ultimate/F-OR1/Teilnehmer/ultimate/V1 - 3Wheeler/Antrieb.SLDASM

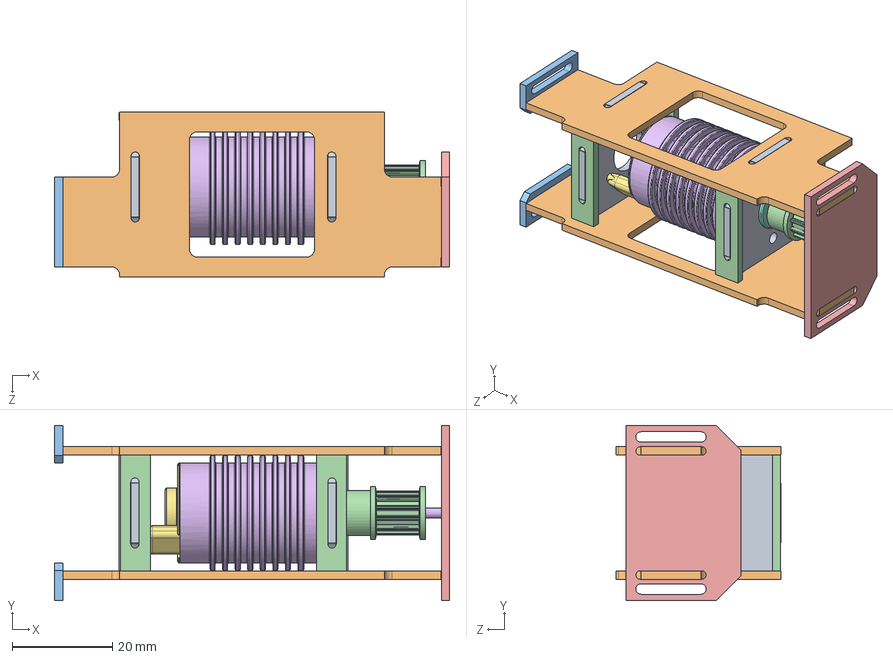
[picture p28: CAD file, 2019-10-27]
Teilnehmer/ultimate/V1 - 3Wheeler/Antrieb.SLDASM
79.0 x 35.0 x 33.0 mm
Rahmen-Antrieb-Platine-Seite x 2
Rahmen-Antrieb-Platine-Oben x 2
Rahmen-Antrieb-Platine-Anschluss2 x 2
Rahmen-Antrieb-Platine-Hinten x 4
Rahmen-Antrieb-Platine-Anschluss1
Motor_B20-30-24S-FIN-Gehaeuse
Motor_B20-30-24S-FIN-FlanschHinten
Motor_B20-30-24S-FIN-FlanschVorne
Motor_B20-30-24S-FIN-Rotorwelle
Motor_B20-30-24S-FIN-Lager x 2
Motor_B20-30-24S-FIN-Masse
Zahnriemenrad T2.5 B6 bis Z20
Antrieb-Reduzierhülse
Antrieb-Dorn
