ultimate/F-OR1/Teilnehmer/ultimate/V1 - 3Wheeler/Fertigung/Rahmen-Antrieb-Flach.SLDASM

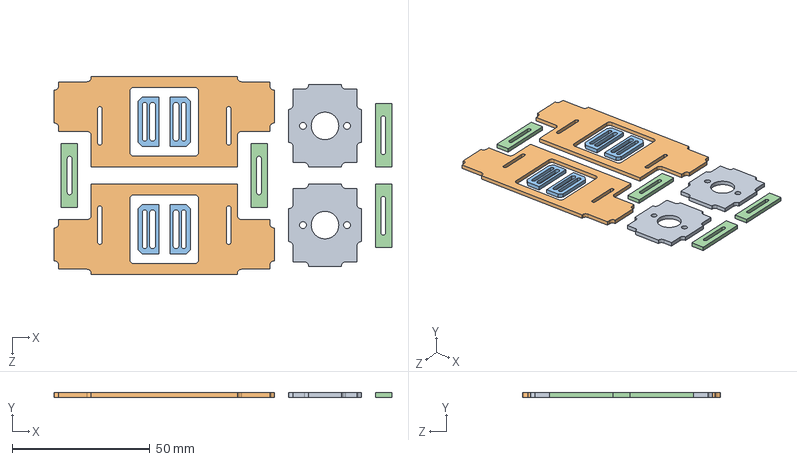
[picture p29: CAD file, 2019-10-27]
Teilnehmer/ultimate/V1 - 3Wheeler/Fertigung/Rahmen-Antrieb-Flach.SLDASM
122.6 x 1.65 x 72.0 mm
Rahmen-Antrieb-Platine-Seite x 2
Rahmen-Antrieb-Platine-Oben x 2
Rahmen-Antrieb-Platine-Anschluss2 x 4
Rahmen-Antrieb-Platine-Hinten x 4
