ultimate/F-OR1/Teilnehmer/ultimate/V2 - Lego/Adapter-Servo-Zahnrad-16Z.SLDASM

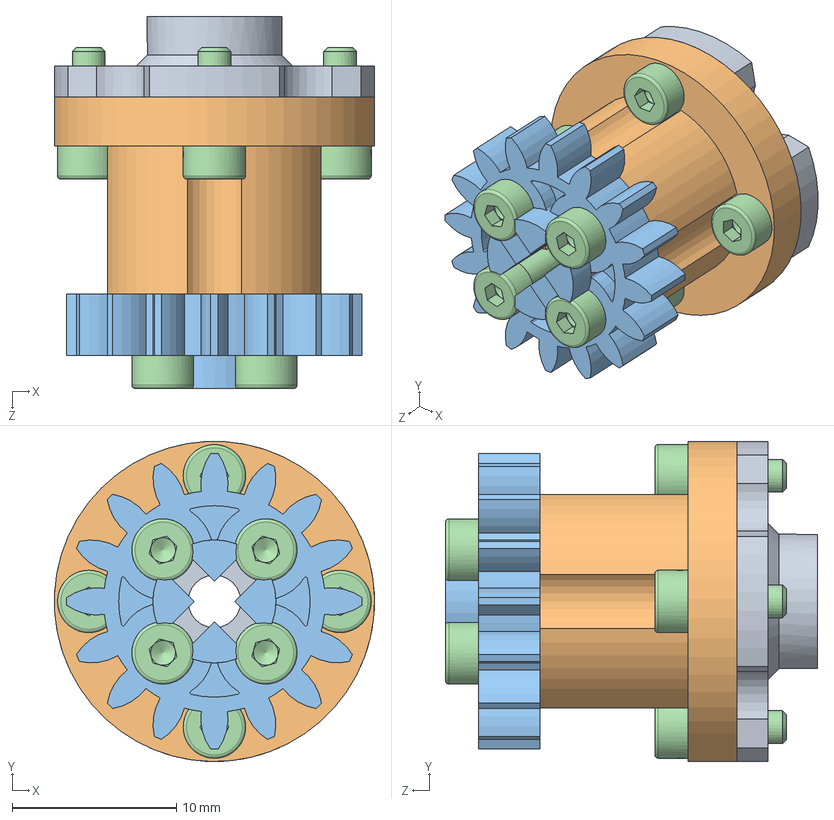
[picture p30: CAD file, 2019-10-27]
Teilnehmer/ultimate/V2 - Lego/Adapter-Servo-Zahnrad-16Z.SLDASM
19.5 x 19.5 x 22.6 mm
Servo-Horn-4er-modifiziert
Adapter-Servo-Zahnrad-16Z
Lego Zahnrad 16Z
DIN 912 M2 x 6 --- 6N x 8
