ultimate/F-OR1/Teilnehmer/ultimate/Test/Kardan.SLDASM

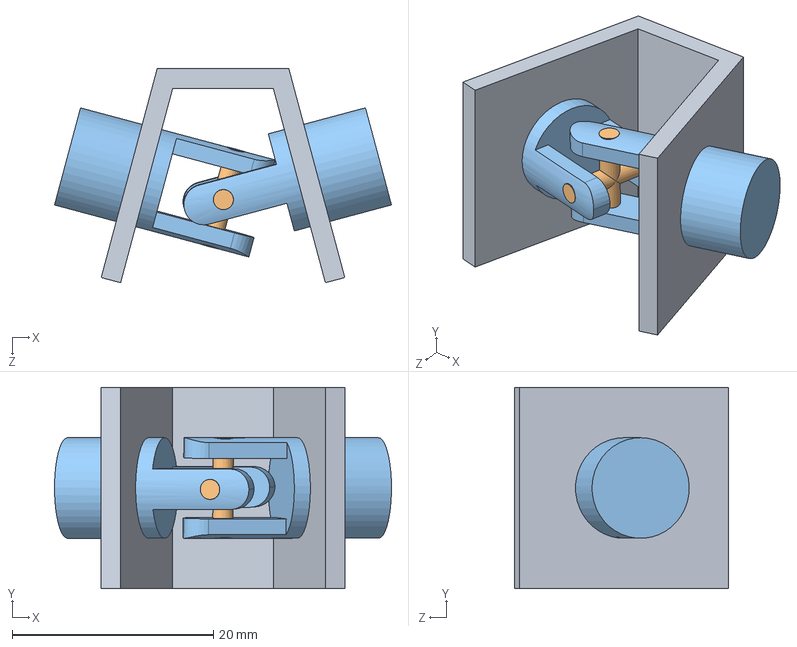
[picture p31: CAD file, 2019-10-27]
Teilnehmer/ultimate/Test/Kardan.SLDASM
33.5 x 20.0 x 21.3 mm
Kardan-Block
Kardan-1
Kardan-2 x 2
