ultimate/F-OR1/Teilnehmer/ultimate/V3 - 4Wheeler/Antrieb.SLDASM

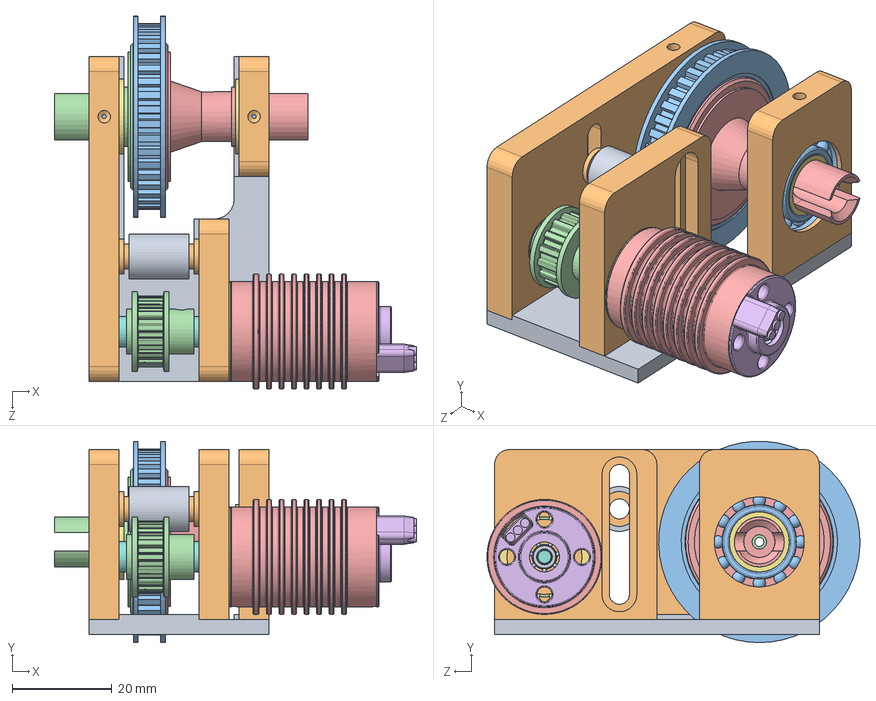
[picture p32: CAD file, 2019-10-27]
Teilnehmer/ultimate/V3 - 4Wheeler/Antrieb.SLDASM
72.4 x 40.3 x 74.6 mm
Antrieb-Rahmen
Antrieb-Lagerbock x 3
Kugellager - 61801 6801 x 2
Kugellager - MR106 x 2
Motor_B20-30-24S-FIN-Gehaeuse
Motor_B20-30-24S-FIN-FlanschHinten
Motor_B20-30-24S-FIN-FlanschVorne
Motor_B20-30-24S-FIN-Rotorwelle
Motor_B20-30-24S-FIN-Lager x 2
Motor_B20-30-24S-FIN-Masse
Kugel-Diff Hobbyking Mission-D Riemenrad
Kugel-Diff Hobbyking Mission-D Achse1
Kugel-Diff Hobbyking Mission-D Achse2
Kugel-Diff Hobbyking Mission-D Laufscheibe x 2
Antrieb-Achse-Lagerhülse x 2
Antrieb-Motorwelle
Antrieb-Spanner-Rolle
Antrieb-Spanner-Lagerhülse x 3
Kugellager - MR74 x 2
Riemenrad Hobbyking Mission-D
