ultimate/F-OR1/Teilnehmer/ultimate/V3 - 4Wheeler/Fertigung/Fraesen1.SLDASM

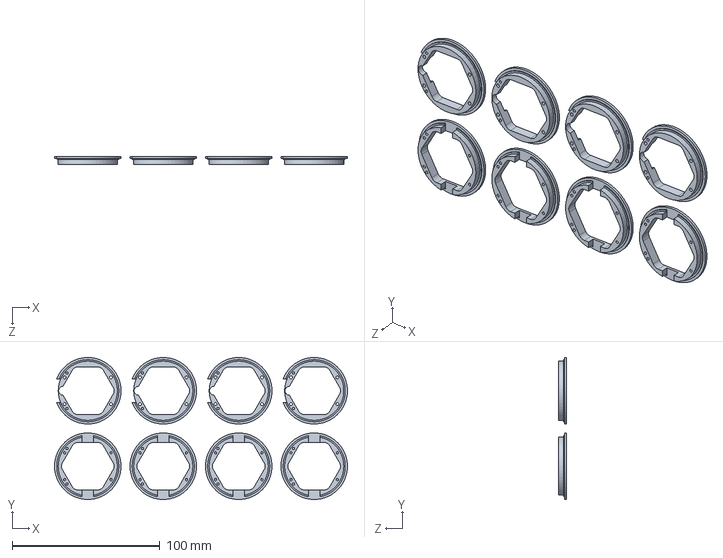
[picture p33: CAD file, 2019-10-27]
Teilnehmer/ultimate/V3 - 4Wheeler/Fertigung/Fraesen1.SLDASM
198.0 x 96.0 x 5.50 mm
Rad-Nabe x 8
