ultimate/F-OR1/Teilnehmer/ultimate/V1 - 3Wheeler/Antrieb-B.SLDASM

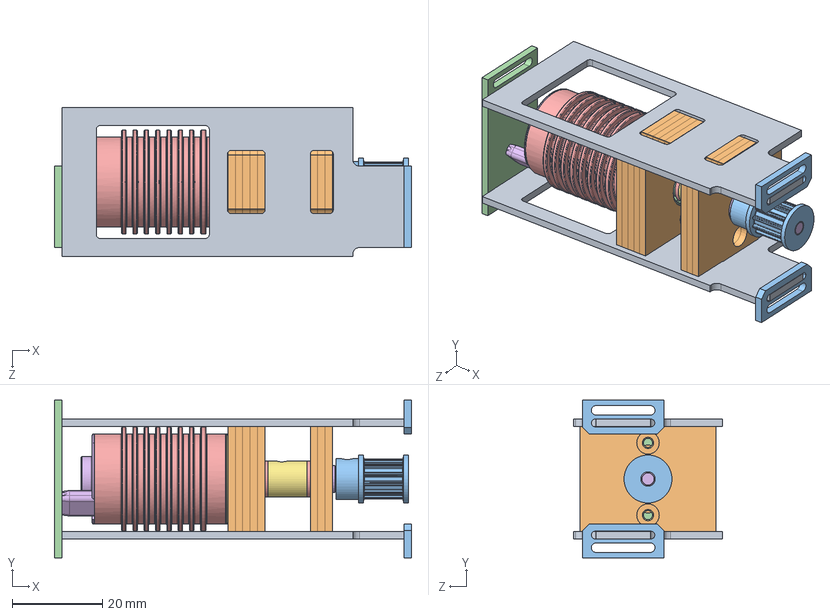
[picture p34: CAD file, 2019-10-27]
Teilnehmer/ultimate/V1 - 3Wheeler/Antrieb-B.SLDASM
79.0 x 34.9 x 33.0 mm
Rahmen-Antrieb-B-Platine-Oben x 2
Rahmen-Antrieb-B-Platine-Seite x 8
Rahmen-Antrieb-B-Platine-Anschluss2 x 2
Rahmen-Antrieb-B-Platine-Anschluss1
Motor_B20-30-24S-FIN-Gehaeuse
Motor_B20-30-24S-FIN-FlanschHinten
Motor_B20-30-24S-FIN-FlanschVorne
Motor_B20-30-24S-FIN-Rotorwelle
Motor_B20-30-24S-FIN-Lager x 2
Motor_B20-30-24S-FIN-Masse
Zahnriemenrad T2.5 B6 bis Z20
Kugellager - MR106 x 2
Antrieb-Passscheibe x 2
Antrieb-B-Welle
Antrieb-B-Passhülse
