ultimate/F-OR1/Teilnehmer/ultimate/Test/Reibrad.SLDASM

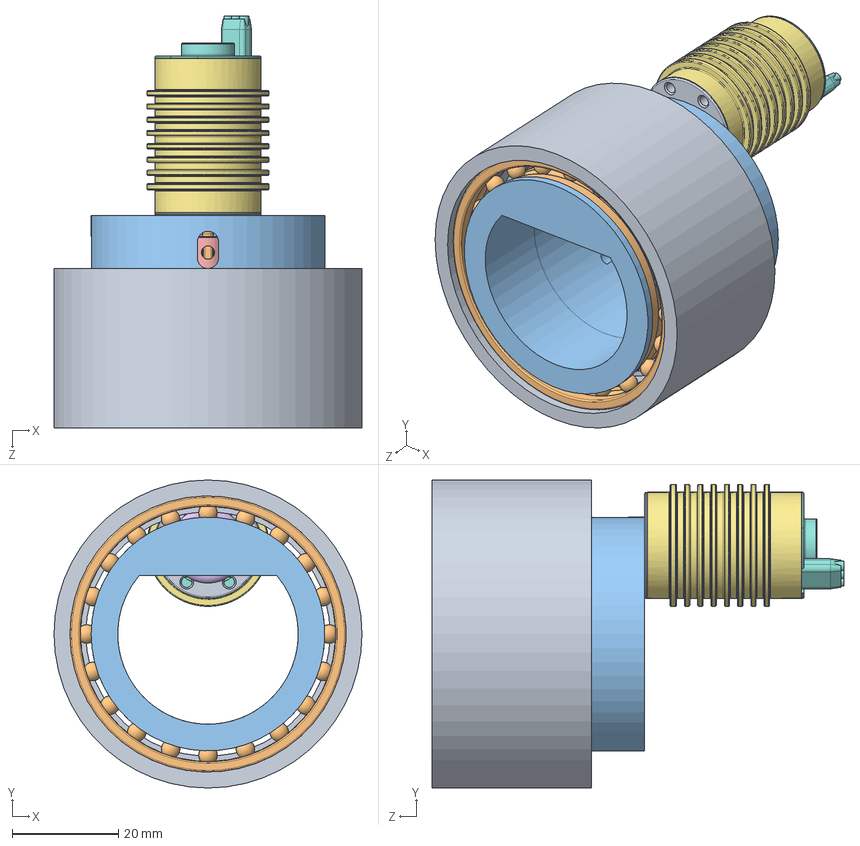
[picture p35: CAD file, 2019-10-27]
Teilnehmer/ultimate/Test/Reibrad.SLDASM
58.0 x 58.0 x 77.5 mm
Reibrad Außenring
Kugellager - 61808 6808 x 2
Reibrad Innenring x 2
Kugellager - MR106 x 2
Reibrad Welle
Reibrad O-Ring
Motor_B20-30-24S-FIN-Gehaeuse
Motor_B20-30-24S-FIN-FlanschHinten
Motor_B20-30-24S-FIN-FlanschVorne
Motor_B20-30-24S-FIN-Rotorwelle
Motor_B20-30-24S-FIN-Lager x 2
Motor_B20-30-24S-FIN-Masse
