ultimate/F-OR1/Teilnehmer/ultimate/V3 - 4Wheeler/Antrieb-Spanner.SLDASM

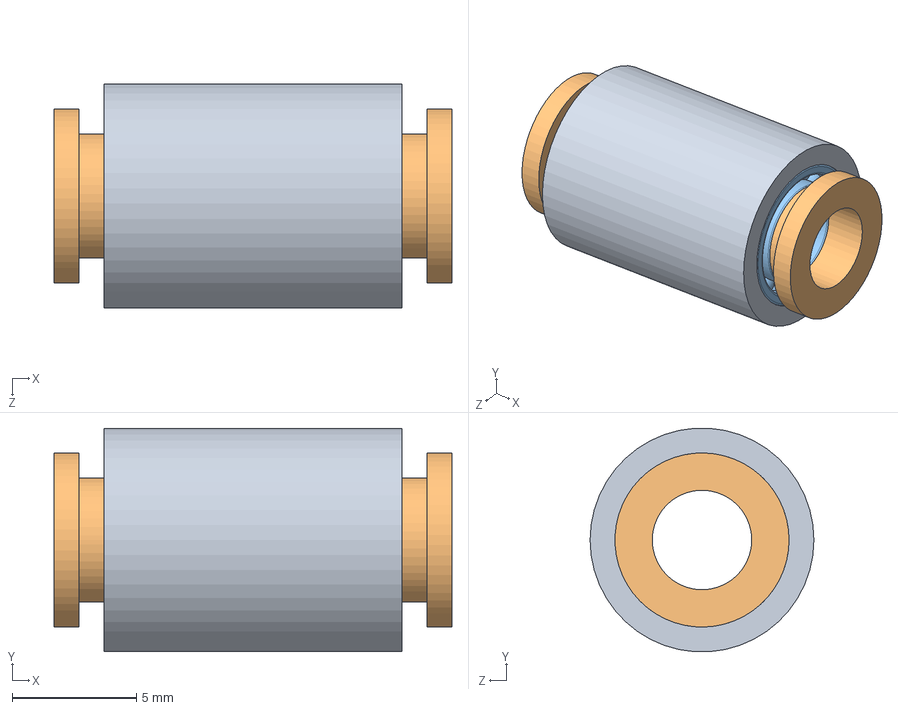
[picture p36: CAD file, 2019-10-27]
Teilnehmer/ultimate/V3 - 4Wheeler/Antrieb-Spanner.SLDASM
16.0 x 8.98 x 9.00 mm
Antrieb-Spanner-Rolle
Antrieb-Spanner-Lagerhülse x 3
Kugellager - MR74 x 2
