ultimate/F-OR1/Teilnehmer/ultimate/V1 - 3Wheeler/Riemen.SLDASM

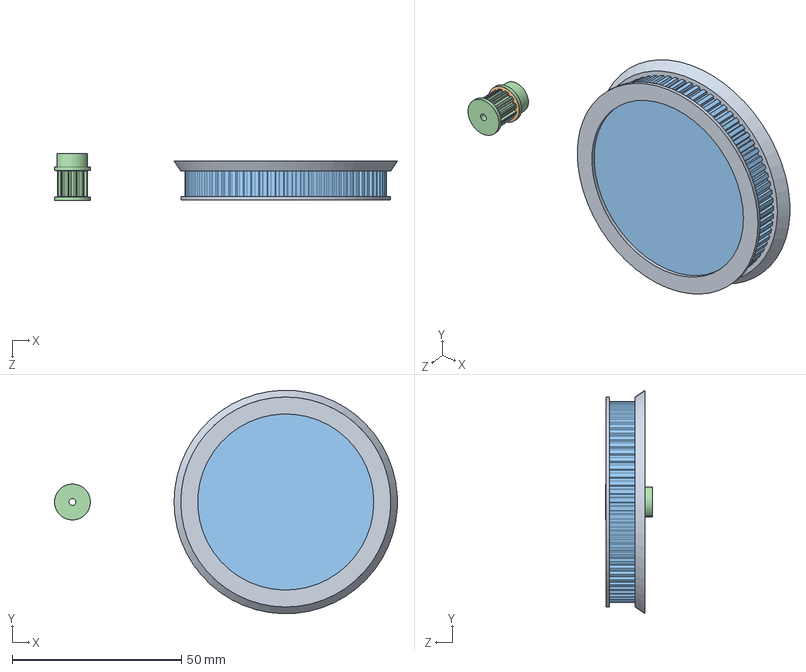
[picture p37: CAD file, 2019-10-27]
Teilnehmer/ultimate/V1 - 3Wheeler/Riemen.SLDASM
101.3 x 66.0 x 14.0 mm
Rad-Hinten-Zahnkranz-Riemen
Zahnriemenrad T2.5 B6 bis Z20
Zahnriemenrad T2.5 B6 Z75 old
Mädler 16051200 Zahnriemenrad T2.5 B6 Z12
