ultimate/F-OR1/Teilnehmer/ultimate/V3 - 4Wheeler/Lenkstange.SLDASM

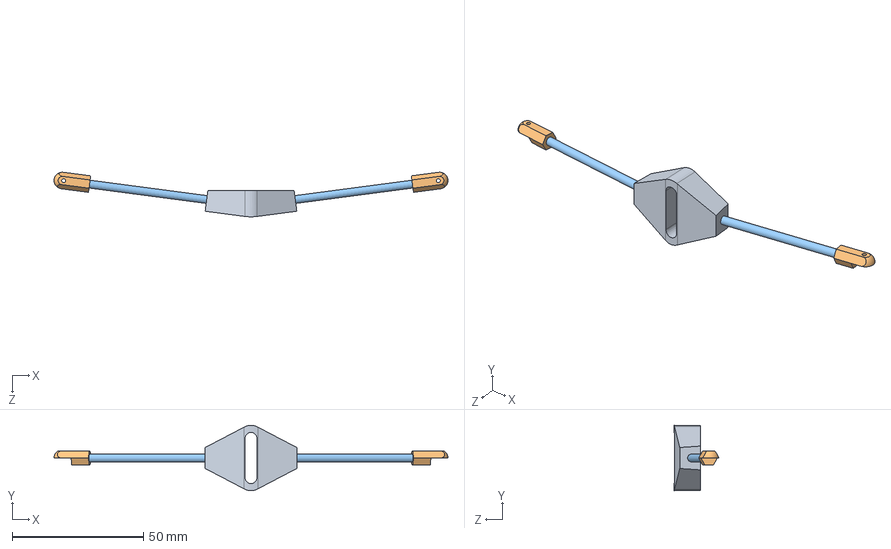
[picture p38: CAD file, 2019-10-27]
Teilnehmer/ultimate/V3 - 4Wheeler/Lenkstange.SLDASM
150.3 x 25.0 x 17.0 mm
Lenkstange-Mittelstück
Gelenkbolzen x 2
Gewindestange x 2
