ultimate/F-OR1/Teilnehmer/ultimate/V1 - 3Wheeler/Lenkstange.SLDASM

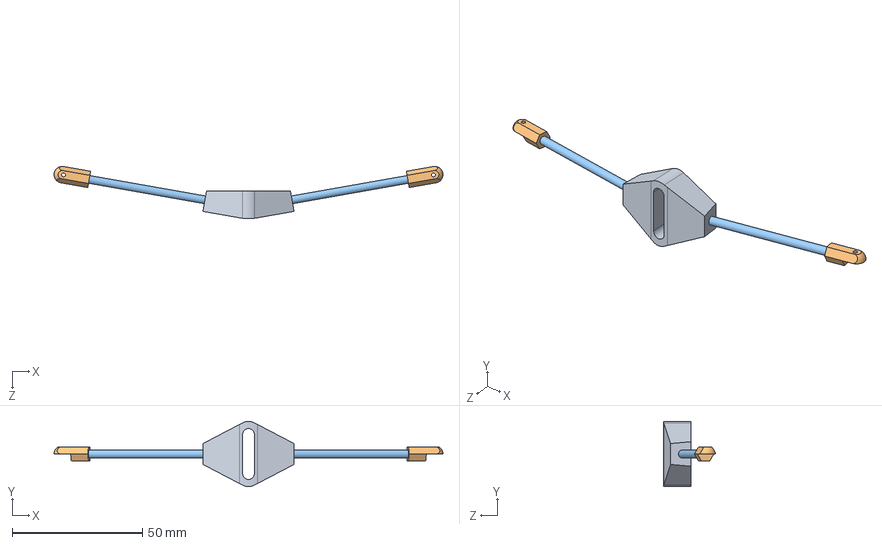
[picture p39: CAD file, 2019-10-27]
Teilnehmer/ultimate/V1 - 3Wheeler/Lenkstange.SLDASM
149.3 x 25.0 x 20.0 mm
Lenkstange-Mittelstück
Gelenkbolzen x 2
Gewindestange x 2
