ultimate/F-OR1/Teilnehmer/ultimate/V1 - 3Wheeler/Druck/Antrieb-Passscheibe.SLDASM

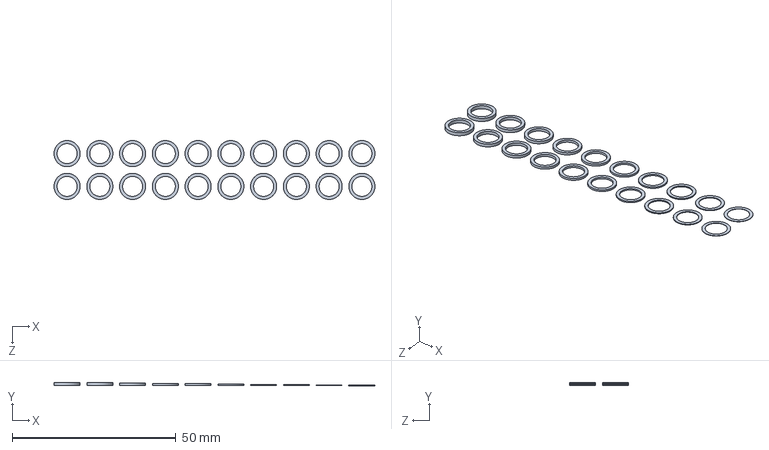
[picture p40: CAD file, 2019-10-27]
Teilnehmer/ultimate/V1 - 3Wheeler/Druck/Antrieb-Passscheibe.SLDASM
98.0 x 1.00 x 18.0 mm
Antrieb-Passscheibe x 20
