ultimate/F-OR1/Teilnehmer/ultimate/V1 - 3Wheeler/Druck/Lager-Montagehilfe-x4.SLDASM

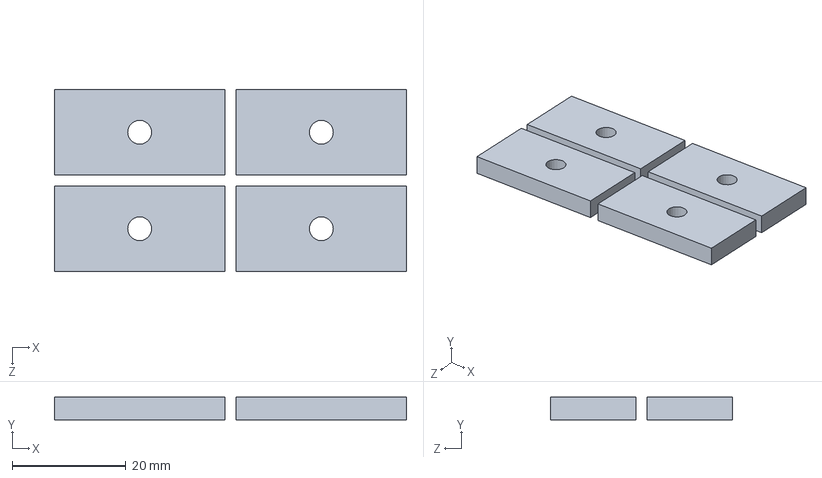
[picture p41: CAD file, 2019-10-27]
Teilnehmer/ultimate/V1 - 3Wheeler/Druck/Lager-Montagehilfe-x4.SLDASM
62.0 x 4.00 x 32.0 mm
Lager-Montagehilfe x 4
