ultimate/F-OR1/Teilnehmer/ultimate/V1 - 3Wheeler/Rad-Vorne.SLDASM

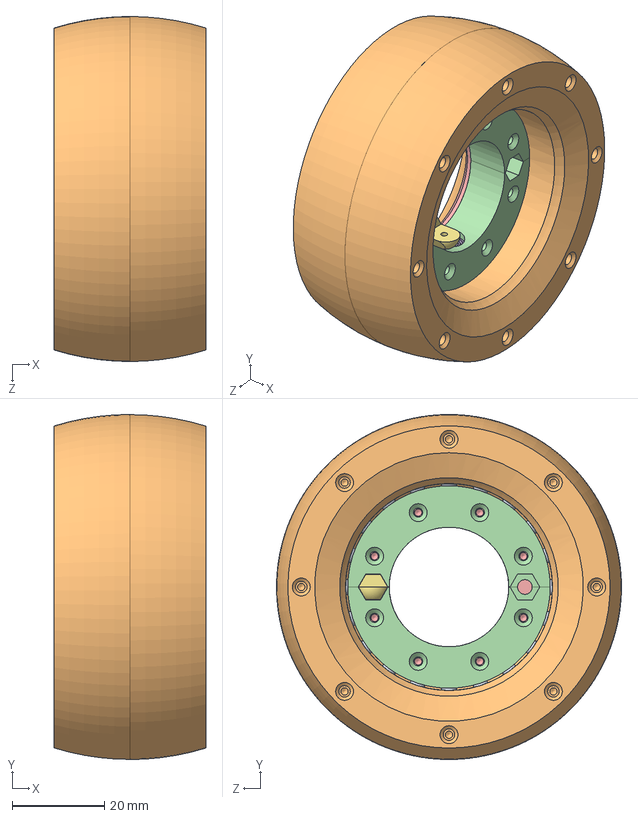
[picture p42: CAD file, 2019-10-27]
Teilnehmer/ultimate/V1 - 3Wheeler/Rad-Vorne.SLDASM
33.0 x 75.0 x 75.0 mm
Kugellager - 61808 6808
Rad-Vorne-Korpus x 2
Lager-Abstandsscheibe x 3
Rad-Vorne-Aufnahme x 2
Rad-Vorne-Innenkranz
Kugellager - MR74 x 2
Gelenkbolzen
