ultimate/F-OR1/Teilnehmer/ultimate/V1 - 3Wheeler/Rahmen-Antrieb.SLDASM

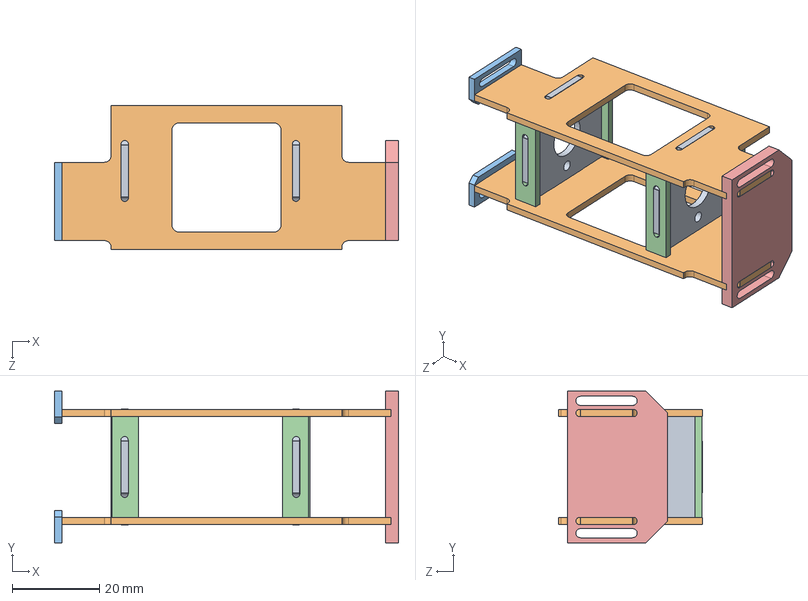
[picture p43: CAD file, 2019-10-27]
Teilnehmer/ultimate/V1 - 3Wheeler/Rahmen-Antrieb.SLDASM
79.0 x 34.9 x 33.0 mm
Rahmen-Antrieb-Platine-Seite x 2
Rahmen-Antrieb-Platine-Oben x 2
Rahmen-Antrieb-Platine-Anschluss2 x 2
Rahmen-Antrieb-Platine-Hinten x 4
Rahmen-Antrieb-Platine-Anschluss1
