ultimate/F-OR1/Teilnehmer/ultimate/V1 - 3Wheeler/Rahmen-Hinten.SLDASM

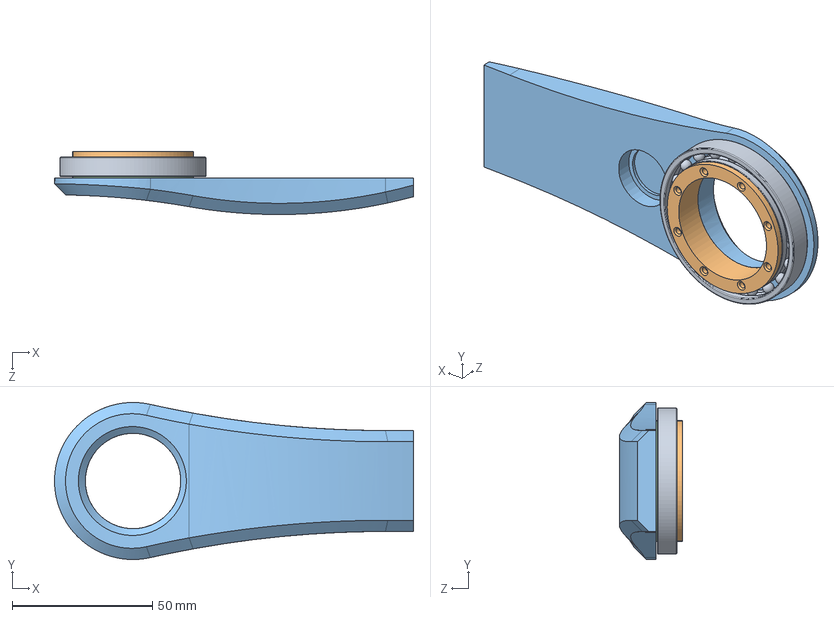
[picture p44: CAD file, 2019-10-27]
Teilnehmer/ultimate/V1 - 3Wheeler/Rahmen-Hinten.SLDASM
128.0 x 56.0 x 22.5 mm
Kugellager - 61808 6808
Rad-Hinten-Aufnahme
Rahmen-Hinten
Lager-Abstandsscheibe
