ultimate/F-OR1/Teilnehmer/ultimate/V1 - 3Wheeler/Rad-Hinten.SLDASM

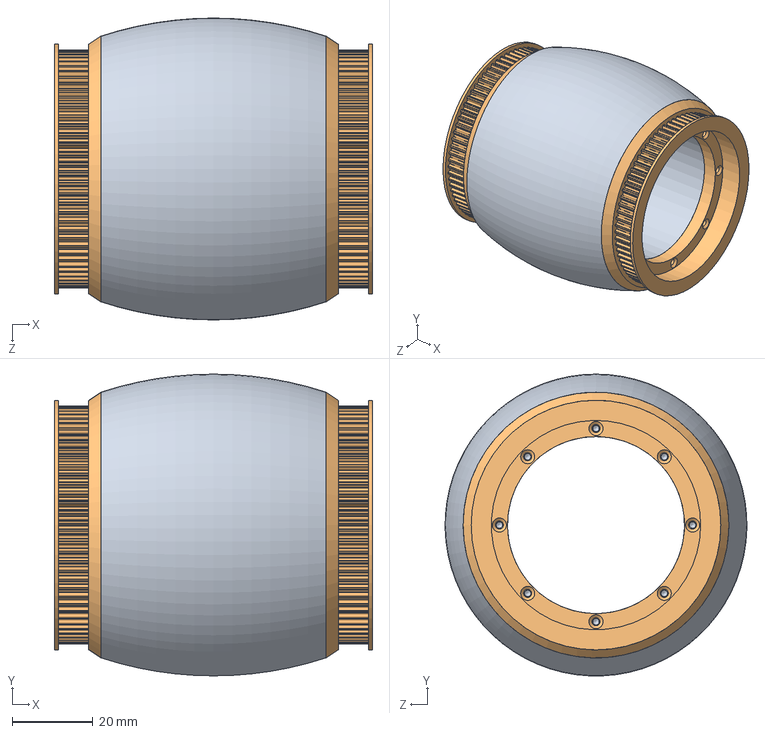
[picture p45: CAD file, 2019-10-27]
Teilnehmer/ultimate/V1 - 3Wheeler/Rad-Hinten.SLDASM
79.0 x 75.0 x 75.0 mm
Rad-Hinten-Korpus
Rad-Hinten-Zahnkranz-Riemen x 2
