ultimate/F-OR1/Teilnehmer/ultimate/V1 - 3Wheeler/Rahmen.SLDASM

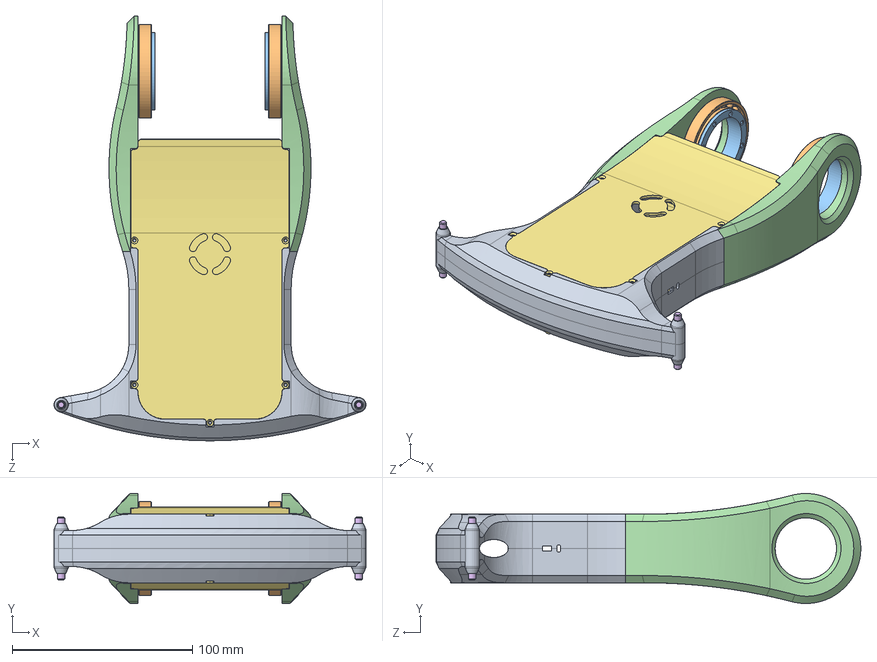
[picture p46: CAD file, 2019-10-27]
Teilnehmer/ultimate/V1 - 3Wheeler/Rahmen.SLDASM
173.0 x 61.0 x 235.5 mm
Rahmen-Vorne x 2
Kugellager - 61808 6808 x 2
Rad-Hinten-Aufnahme x 2
Rahmen-Hinten x 2
Lager-Abstandsscheibe x 2
Achse 4mm x 2
Blech-Abdeckung
Rahmen-Versteifung-Vorne
Rahmen-Servo
