ultimate/F-OR1/Komponenten/Kugel-Diff Hobbyking Mission-D Achse2.SLDPRT

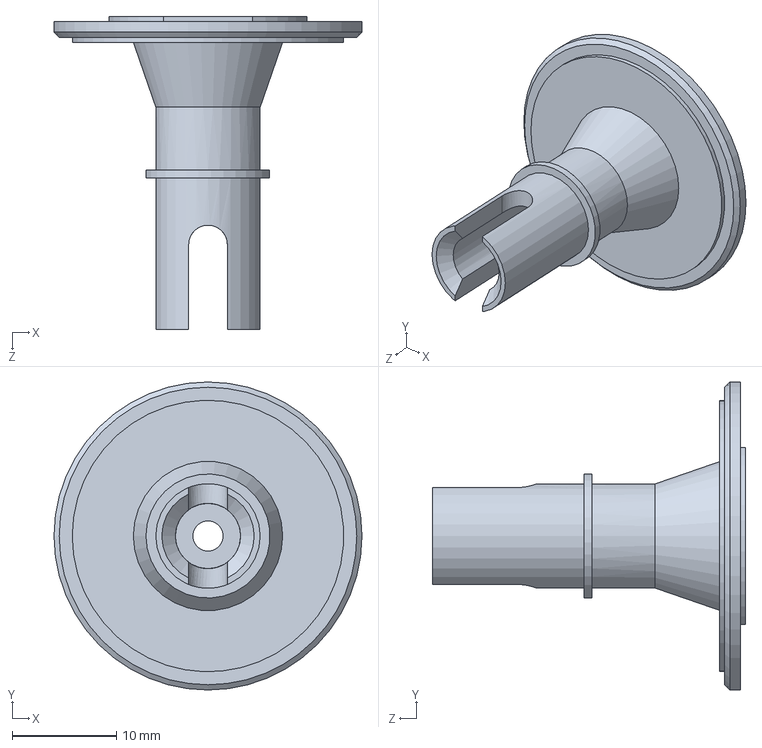
[picture p47: CAD file, 2019-10-27]
Komponenten/Kugel-Diff Hobbyking Mission-D Achse2.SLDPRT
29.5 x 29.5 x 30.0 mm
