ultimate/F-OR1/Komponenten/Step/Hobby King X-Car 60A Brushless Car ESC.STEP

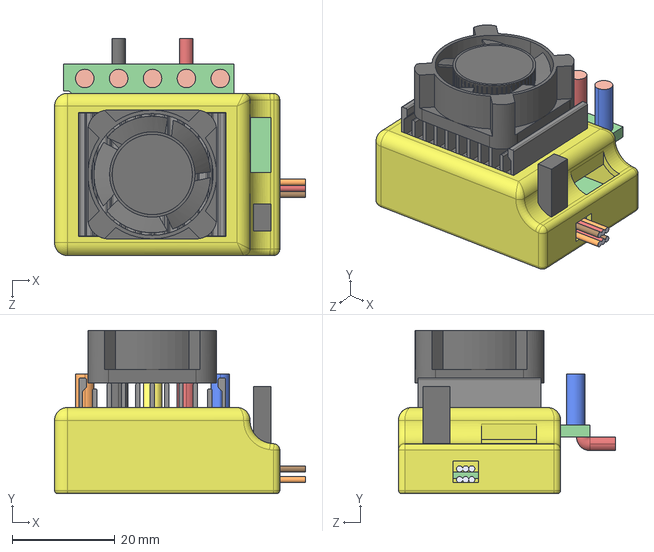
[picture p48: CAD file, 2014-06-05]
Komponenten/Step/Hobby King X-Car 60A Brushless Car ESC.STEP
48.9 x 31.8 x 42.3 mm
Hobby King X-Car 60A Brushless Car ESC
Hobby King X-Car 60A Brushless Car ESC - Lüfter
