ultimate/F-OR1/Normteile/Kugellager - 61800 6800.SLDPRT

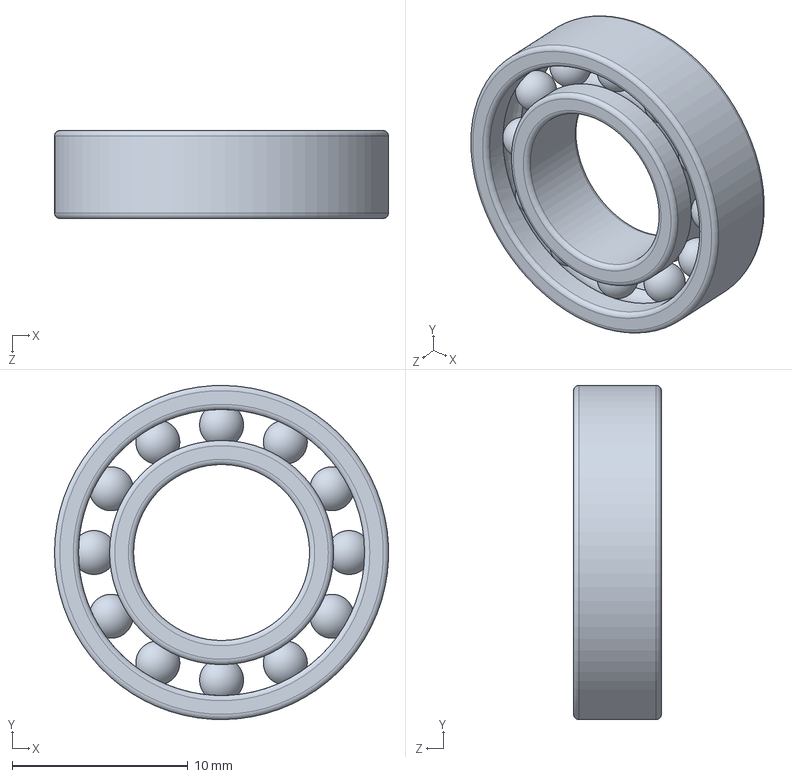
[picture p49: CAD file, 2019-10-27]
Normteile/Kugellager - 61800 6800.SLDPRT
19.0 x 19.0 x 5.00 mm
