ultimate/F-OR1/Normteile/Step/Mädler 16057200.stp

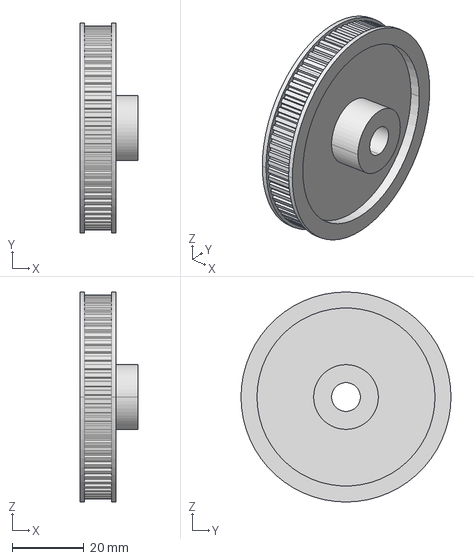
[picture p50: CAD file, 2019-10-27]
Normteile/Step/Mädler 16057200.stp
16.0 x 58.4 x 58.4 mm
