ultimate/F-OR1/Teilnehmer/ultimate/Test/Druck/Reibrad Innenring 1.STL

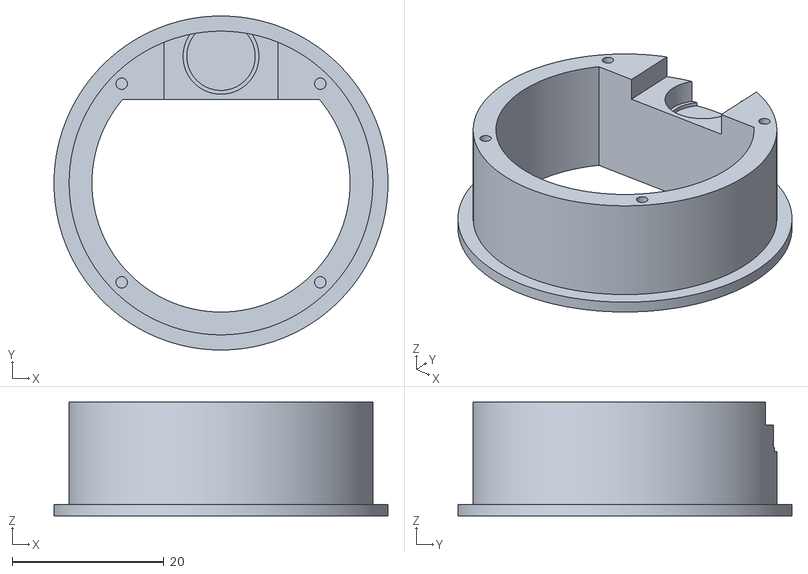
[picture p51: CAD file, 2019-10-27]
Teilnehmer/ultimate/Test/Druck/Reibrad Innenring 1.STL
44.0 x 44.0 x 15.0
