ultimate/F-OR1/Teilnehmer/ultimate/Test/Reibrad Innenring.SLDPRT

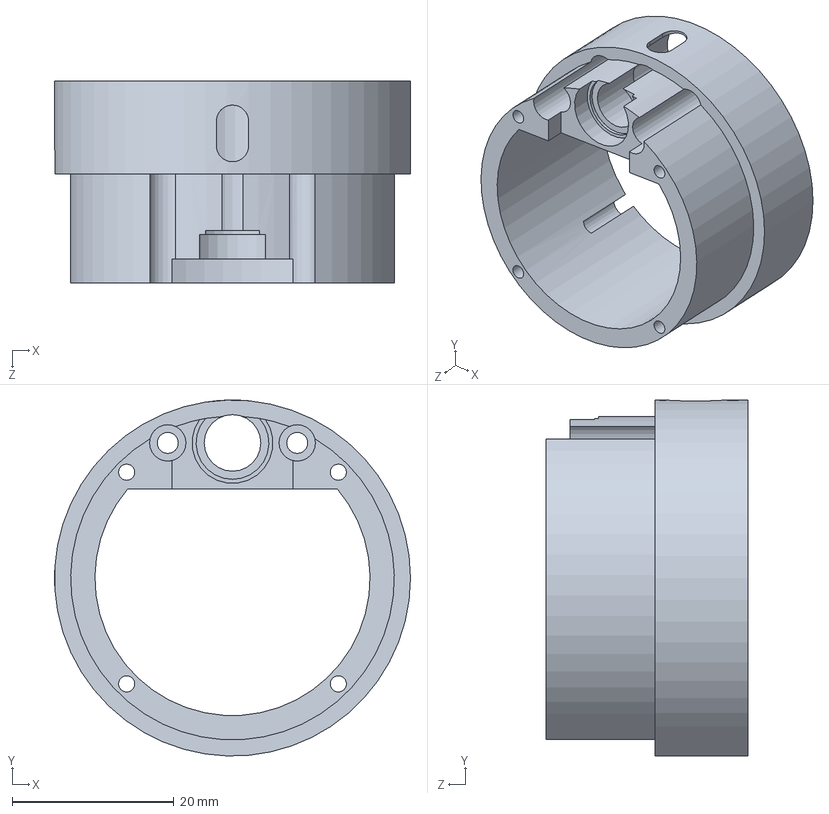
[picture p52: CAD file, 2019-10-27]
Teilnehmer/ultimate/Test/Reibrad Innenring.SLDPRT
44.0 x 44.0 x 25.0 mm
