ultimate/F-OR1/Teilnehmer/ultimate/V1 - 3Wheeler/Antrieb-Achsfixierung.SLDPRT

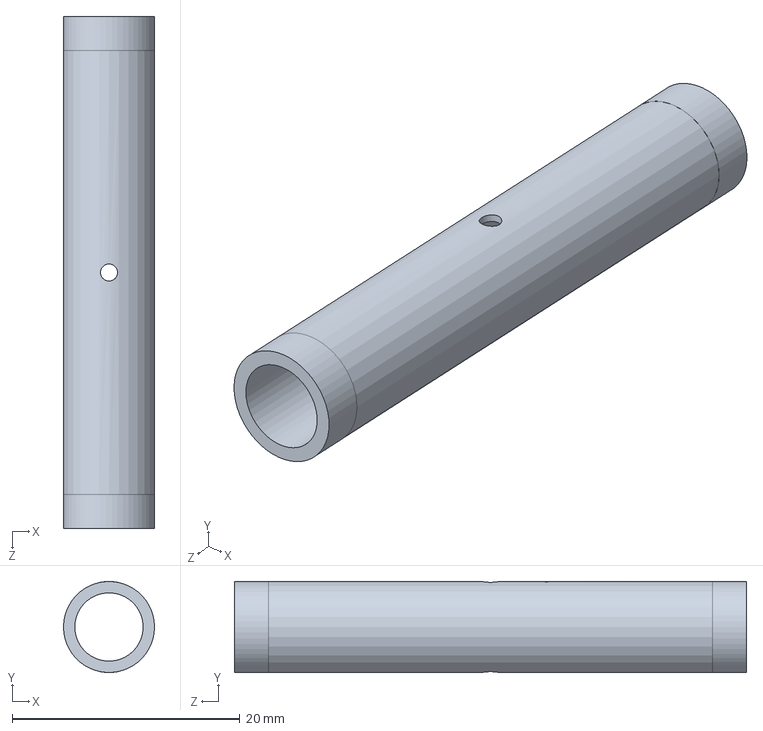
[picture p53: CAD file, 2019-10-27]
Teilnehmer/ultimate/V1 - 3Wheeler/Antrieb-Achsfixierung.SLDPRT
8.00 x 8.00 x 45.0 mm
