ultimate/F-OR1/Teilnehmer/ultimate/V1 - 3Wheeler/Druck/Zahnrad 0.5M 40T.STL

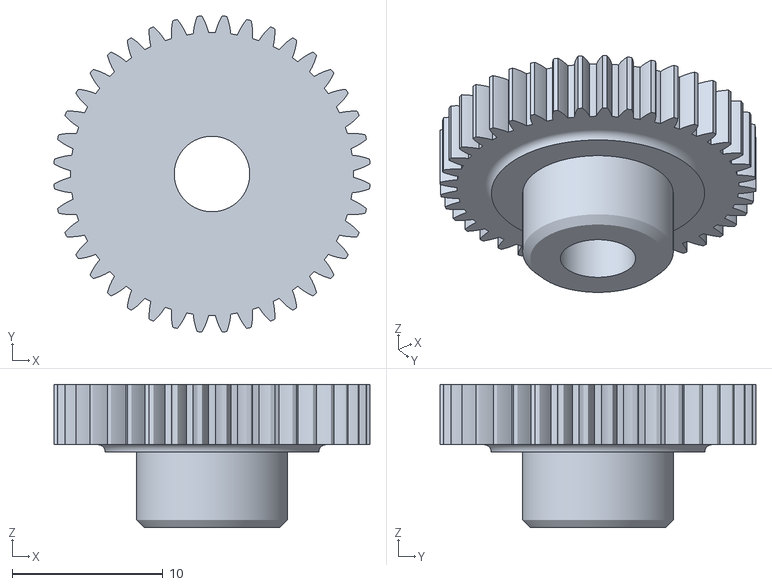
[picture p54: CAD file, 2019-10-27]
Teilnehmer/ultimate/V1 - 3Wheeler/Druck/Zahnrad 0.5M 40T.STL
21.0 x 21.0 x 9.50
