ultimate/F-OR1/Teilnehmer/ultimate/V1 - 3Wheeler/Fertigung/Blech-Abdeckung - mit Lüftung.DXF

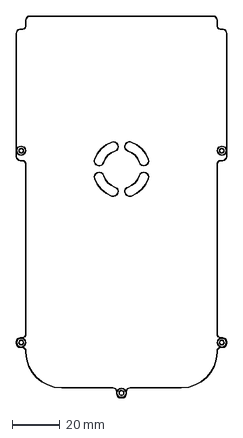
[picture p55: CAD file, 2019-10-27]
Teilnehmer/ultimate/V1 - 3Wheeler/Fertigung/Blech-Abdeckung - mit Lüftung.DXF
87.8 x 159.5 mm
