ultimate/F-OR1/Teilnehmer/ultimate/V2 - Lego/Aufnahme-Motoren.SLDPRT

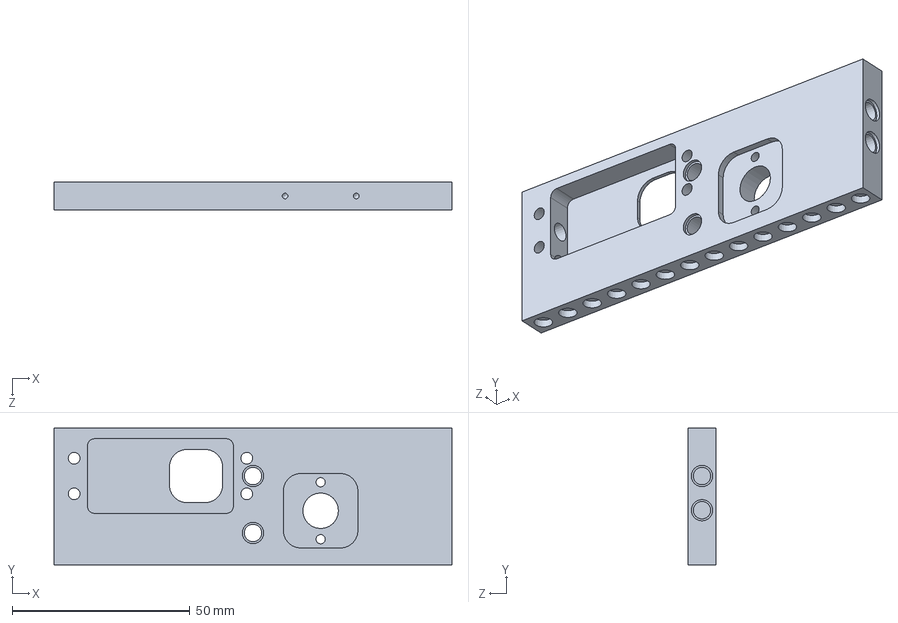
[picture p56: CAD file, 2019-10-27]
Teilnehmer/ultimate/V2 - Lego/Aufnahme-Motoren.SLDPRT
111.8 x 38.4 x 8.00 mm
