ultimate/F-OR1/Teilnehmer/ultimate/V3 - 4Wheeler/Export/4-Wheeler - Rad-2 Rad-Lagersitz-2.STL

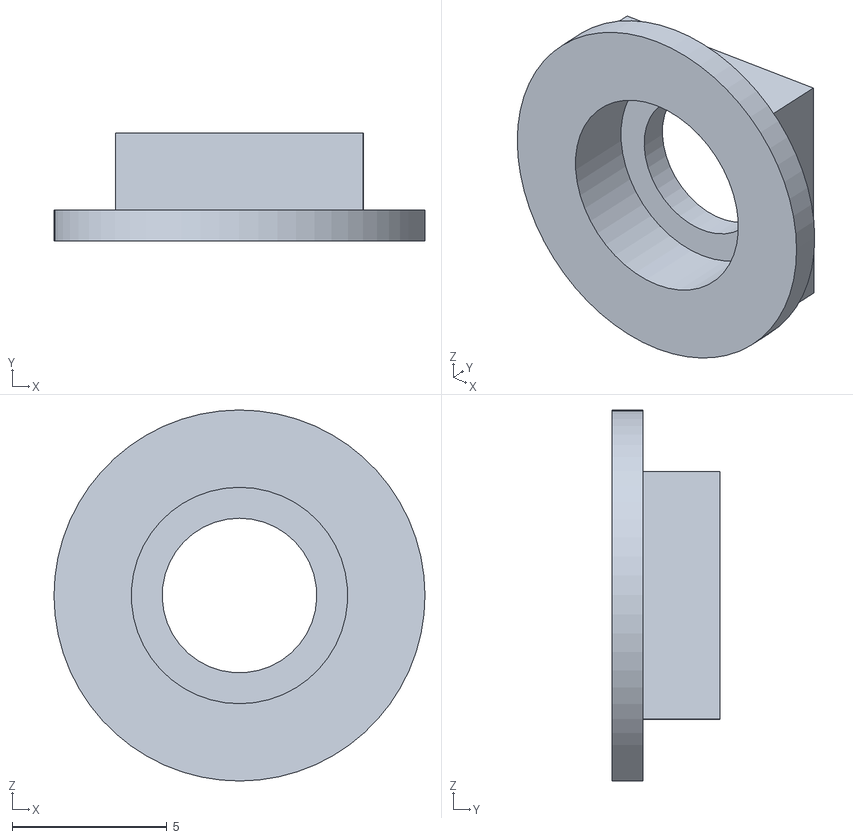
[picture p57: CAD file, 2020-09-06]
Teilnehmer/ultimate/V3 - 4Wheeler/Export/4-Wheeler - Rad-2 Rad-Lagersitz-2.STL
12.0 x 3.50 x 12.0
