ultimate/F-OR1/Teilnehmer/ultimate/V3 - 4Wheeler/Fertigung/Rad-Adapter-Hinten.DXF

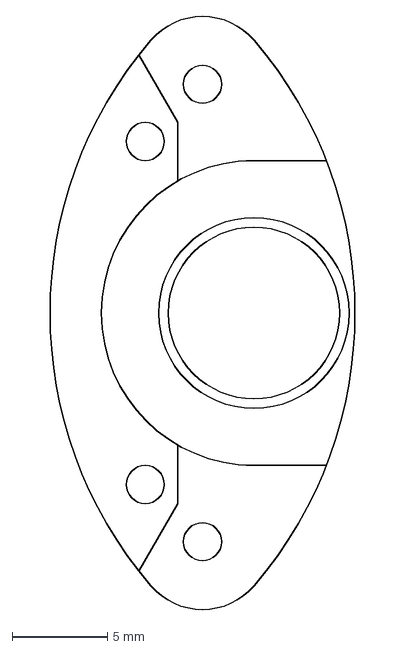
[picture p58: CAD file, 2019-10-27]
Teilnehmer/ultimate/V3 - 4Wheeler/Fertigung/Rad-Adapter-Hinten.DXF
19.5 x 31.1 mm
