ultimate/F-OR1/Teilnehmer/ultimate/V3 - 4Wheeler/Lenkstange-Mittelstück.SLDPRT

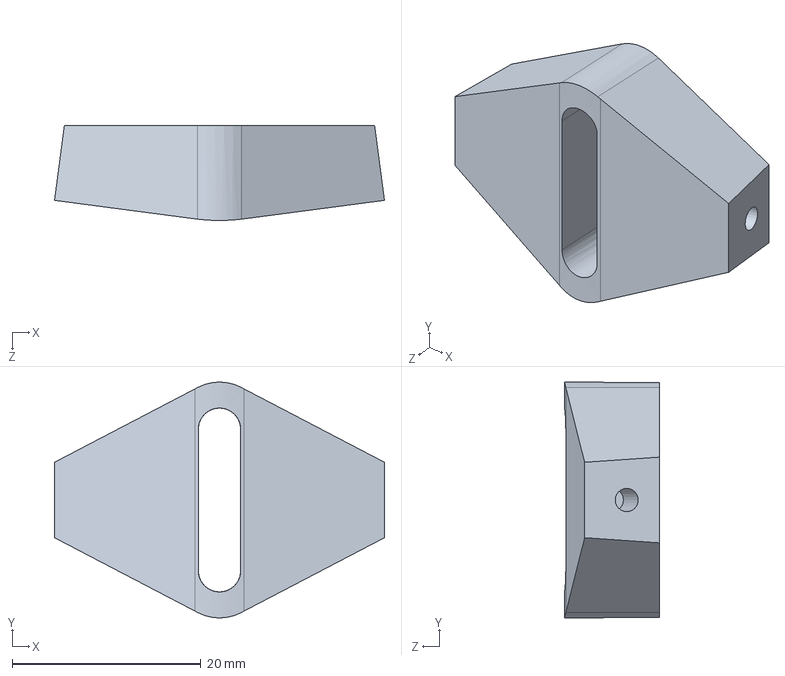
[picture p59: CAD file, 2019-10-27]
Teilnehmer/ultimate/V3 - 4Wheeler/Lenkstange-Mittelstück.SLDPRT
35.0 x 25.0 x 10.1 mm
