ultimate/F-OR1/Komponenten/Step/Hobby King X-Car 60A Brushless Car ESC - Schalter.STEP

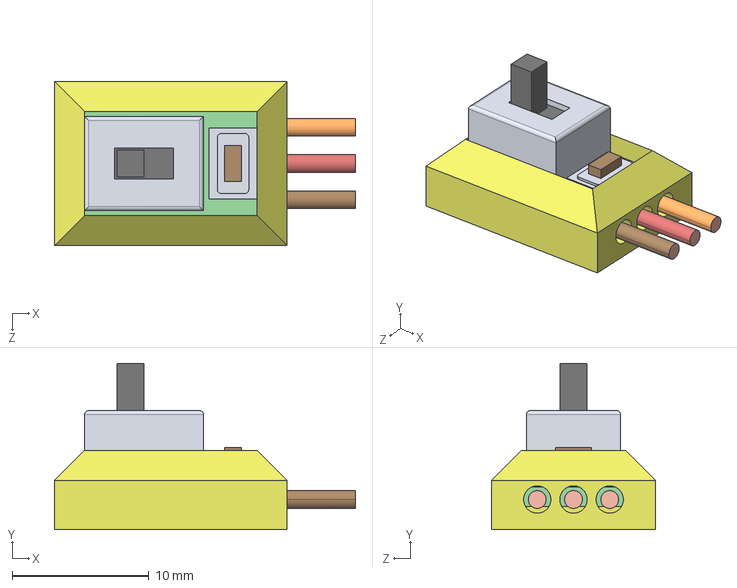
[picture p60: CAD file, 2014-06-05]
Komponenten/Step/Hobby King X-Car 60A Brushless Car ESC - Schalter.STEP
22.0 x 12.2 x 12.0 mm
