ultimate/F-OR1/Normteile/Step/Mädler 16051200.stp

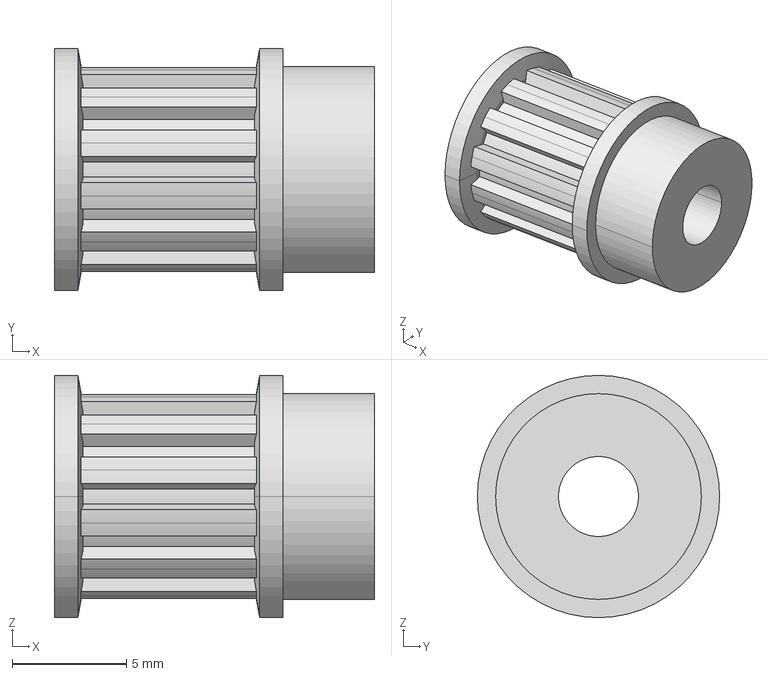
[picture p61: CAD file, 2019-10-27]
Normteile/Step/Mädler 16051200.stp
14.0 x 10.6 x 10.6 mm
