ultimate/F-OR1/Normteile/Zahnrad 1.0M 16T.SLDPRT

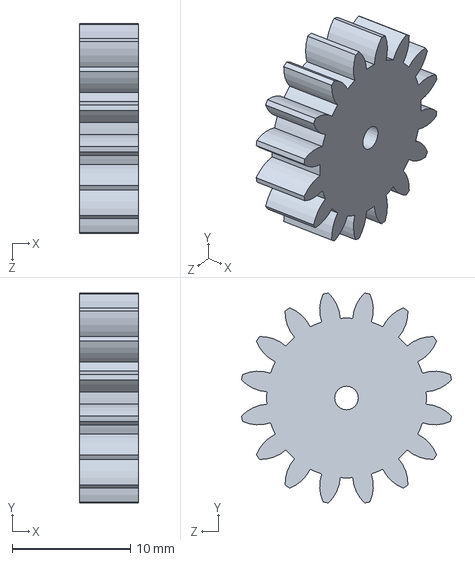
[picture p62: CAD file, 2019-10-27]
Normteile/Zahnrad 1.0M 16T.SLDPRT
5.00 x 17.7 x 17.7 mm
