ultimate/F-OR1/Teilnehmer/ultimate/Test/Reibrad Welle.SLDPRT

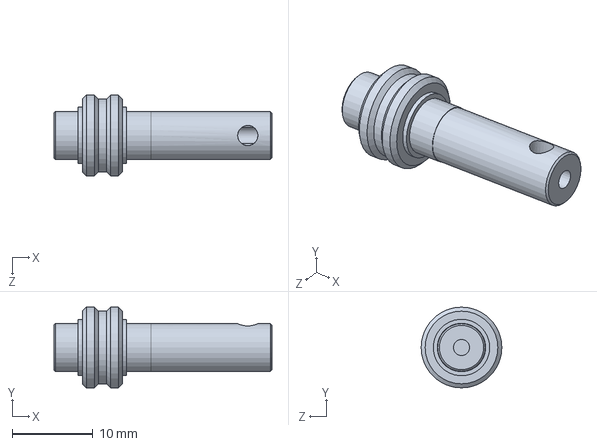
[picture p63: CAD file, 2019-10-27]
Teilnehmer/ultimate/Test/Reibrad Welle.SLDPRT
27.0 x 10.0 x 10.0 mm
