ultimate/F-OR1/Teilnehmer/ultimate/V1 - 3Wheeler/Druck/Zahnrad 0.5M 19T.STL

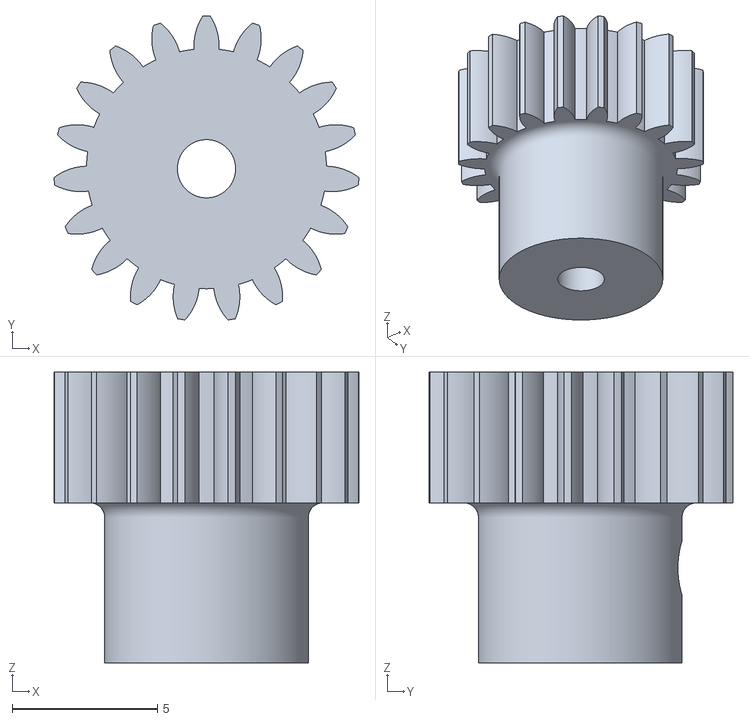
[picture p64: CAD file, 2019-10-27]
Teilnehmer/ultimate/V1 - 3Wheeler/Druck/Zahnrad 0.5M 19T.STL
10.5 x 10.4 x 10.0
