ultimate/F-OR1/Teilnehmer/ultimate/V1 - 3Wheeler/Fertigung/Rahmen-Antrieb-Platine-Anschluss1.DXF

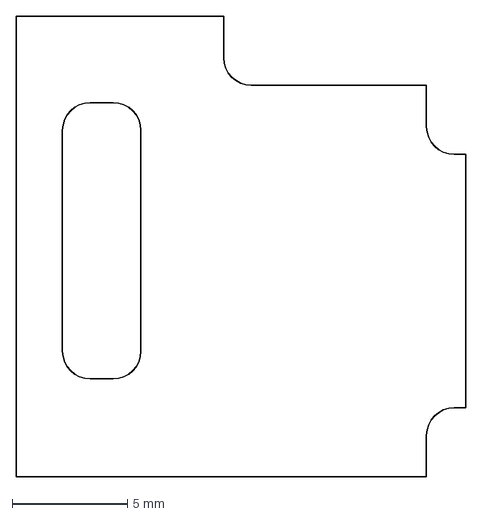
[picture p65: CAD file, 2019-10-27]
Teilnehmer/ultimate/V1 - 3Wheeler/Fertigung/Rahmen-Antrieb-Platine-Anschluss1.DXF
19.5 x 20.0 mm
