ultimate/F-OR1/Teilnehmer/ultimate/V1 - 3Wheeler/Rahmen-Antrieb-Platine-Hinten.SLDPRT

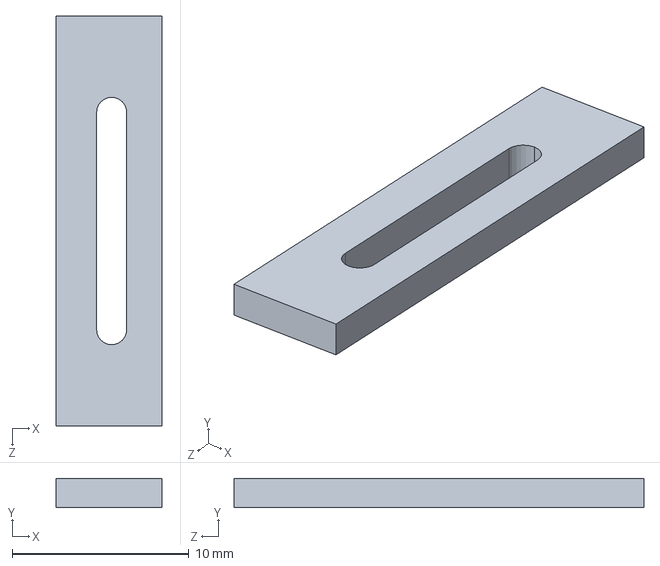
[picture p66: CAD file, 2019-10-27]
Teilnehmer/ultimate/V1 - 3Wheeler/Rahmen-Antrieb-Platine-Hinten.SLDPRT
6.00 x 1.65 x 23.2 mm
