ultimate/F-OR1/Teilnehmer/ultimate/V3 - 4Wheeler/Fertigung/Rahmen-Verkleidung-Vorne.STL

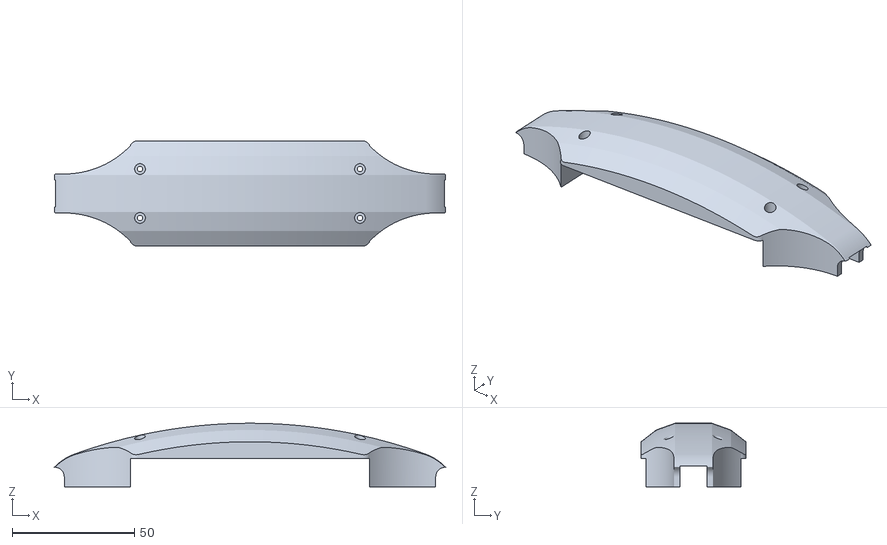
[picture p68: CAD file, 2019-10-27]
Teilnehmer/ultimate/V3 - 4Wheeler/Fertigung/Rahmen-Verkleidung-Vorne.STL
160.0 x 43.0 x 26.0
