ultimate/F-OR1/Komponenten/Schalter.SLDPRT

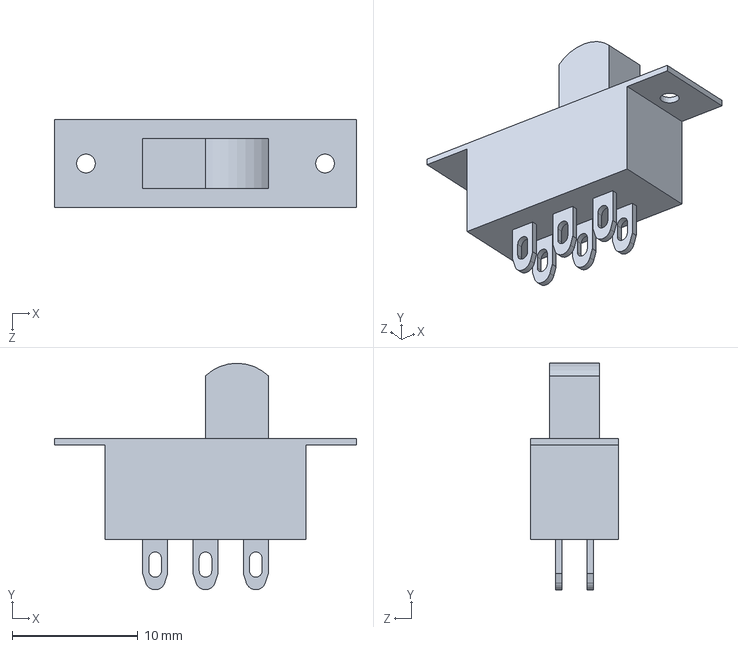
[picture p69: CAD file, 2019-10-27]
Komponenten/Schalter.SLDPRT
24.0 x 18.0 x 7.00 mm
