ultimate/F-OR1/Komponenten/Step/Hobby King X-Car 60A Brushless Car ESC - Kondensator.STEP

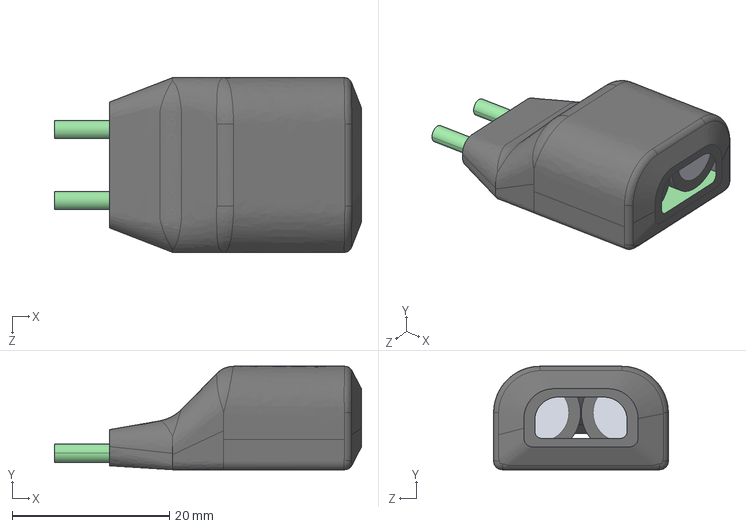
[picture p70: CAD file, 2014-06-05]
Komponenten/Step/Hobby King X-Car 60A Brushless Car ESC - Kondensator.STEP
39.0 x 13.2 x 22.2 mm
