ultimate/F-OR1/Normteile/Step/Mädler 16052000.stp

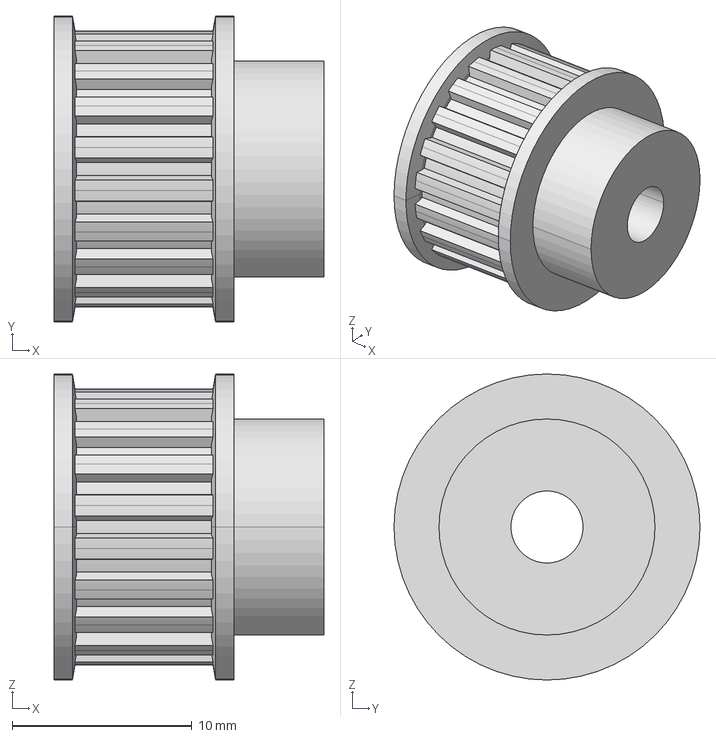
[picture p71: CAD file, 2019-10-27]
Normteile/Step/Mädler 16052000.stp
15.0 x 17.0 x 17.0 mm
