ultimate/F-OR1/Normteile/Welle 6mm.SLDPRT

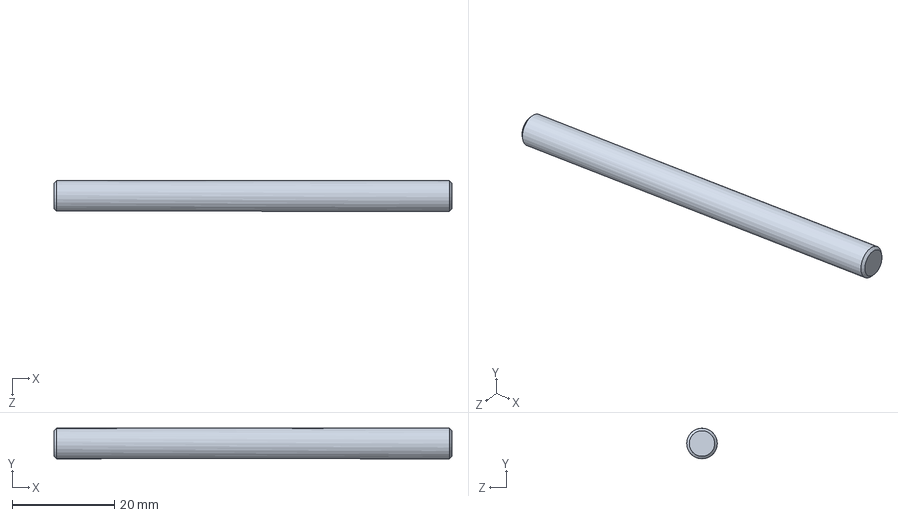
[picture p72: CAD file, 2019-10-27]
Normteile/Welle 6mm.SLDPRT
78.0 x 5.99 x 6.00 mm
