ultimate/F-OR1/Teilnehmer/ultimate/Test/Druck/Reibrad Außenring.STL

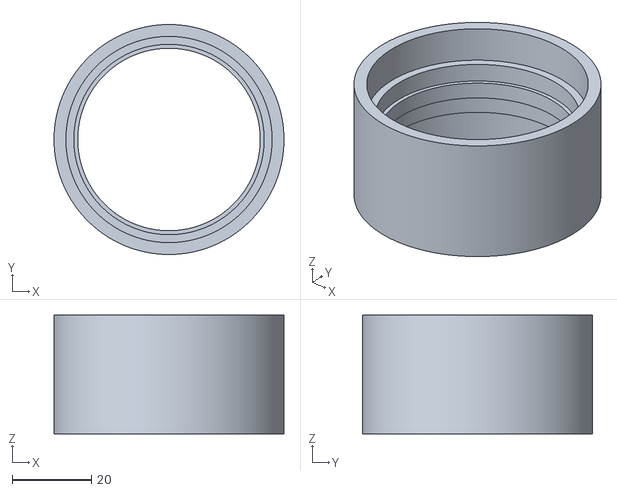
[picture p73: CAD file, 2019-10-27]
Teilnehmer/ultimate/Test/Druck/Reibrad Außenring.STL
58.0 x 58.0 x 30.0
