ultimate/F-OR1/Teilnehmer/ultimate/Test/Planetengetriebe Steg.SLDPRT

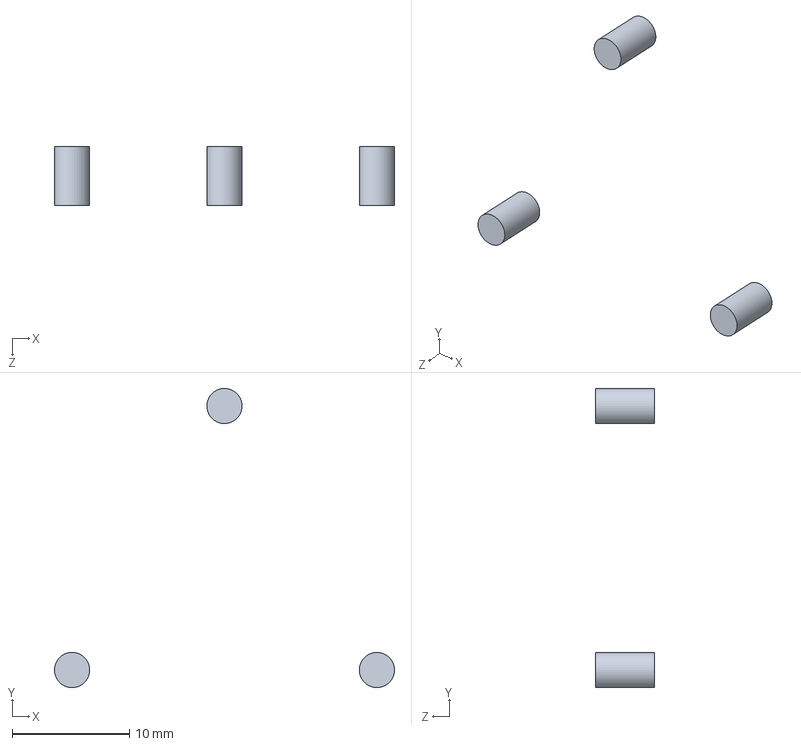
[picture p74: CAD file, 2019-10-27]
Teilnehmer/ultimate/Test/Planetengetriebe Steg.SLDPRT
29.0 x 25.5 x 5.00 mm
