ultimate/F-OR1/Teilnehmer/ultimate/V0 - draft/draft_frame.SLDPRT

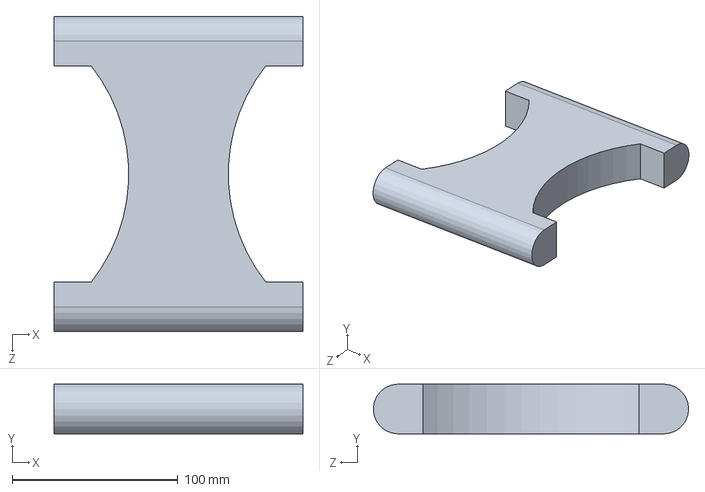
[picture p75: CAD file, 2019-10-27]
Teilnehmer/ultimate/V0 - draft/draft_frame.SLDPRT
150.0 x 30.0 x 190.0 mm
