ultimate/F-OR1/Teilnehmer/ultimate/V1 - 3Wheeler/Druck/Lager-Montagehilfe.STL

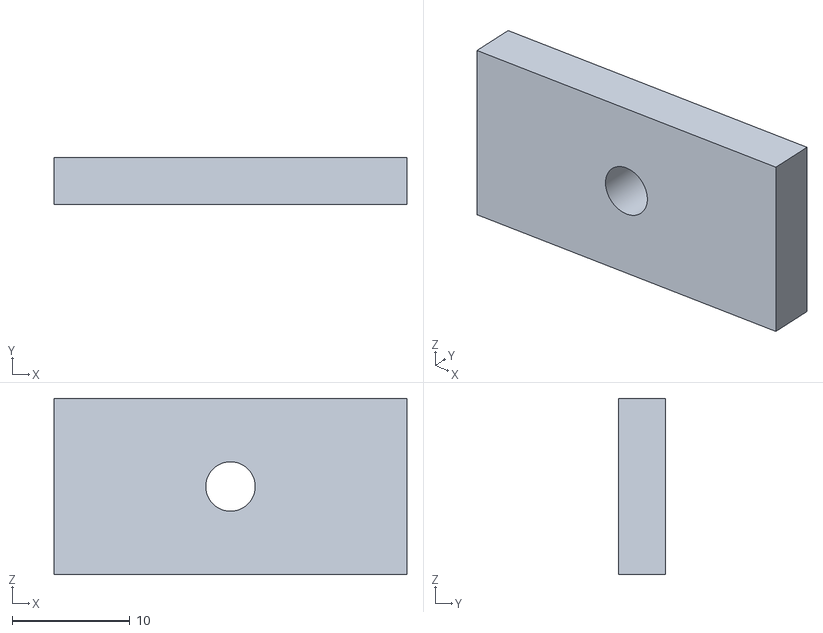
[picture p76: CAD file, 2019-10-27]
Teilnehmer/ultimate/V1 - 3Wheeler/Druck/Lager-Montagehilfe.STL
30.0 x 4.00 x 15.0
