ultimate/F-OR1/Teilnehmer/ultimate/V1 - 3Wheeler/Fertigung/Rahmen-Antrieb-Platine-Seite1.DXF

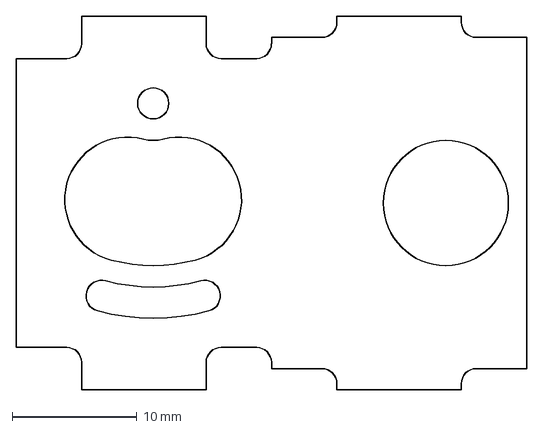
[picture p77: CAD file, 2019-10-27]
Teilnehmer/ultimate/V1 - 3Wheeler/Fertigung/Rahmen-Antrieb-Platine-Seite1.DXF
41.0 x 30.0 mm
