ultimate/F-OR1/Teilnehmer/ultimate/V2 - Lego/Lego Zahnrad 24Z.SLDPRT

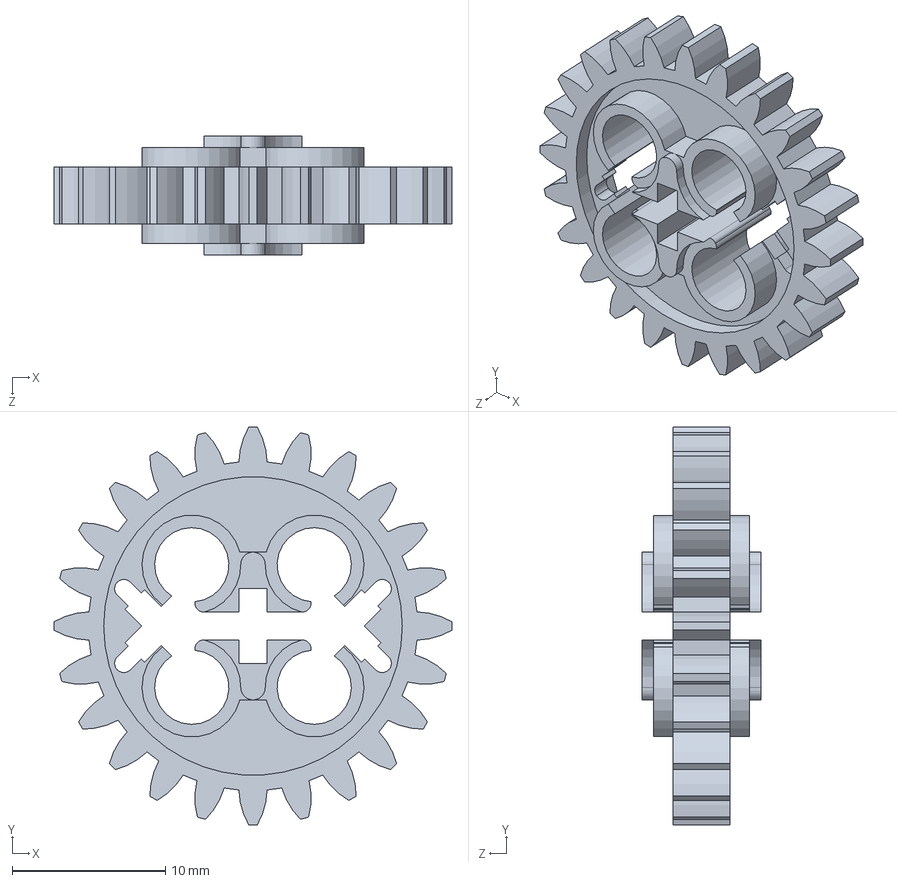
[picture p78: CAD file, 2019-10-27]
Teilnehmer/ultimate/V2 - Lego/Lego Zahnrad 24Z.SLDPRT
26.0 x 26.0 x 7.75 mm
