ultimate/F-OR1/Teilnehmer/ultimate/V3 - 4Wheeler/Export/4-Wheeler - Rad-1 Rad-Nabe-2.STL

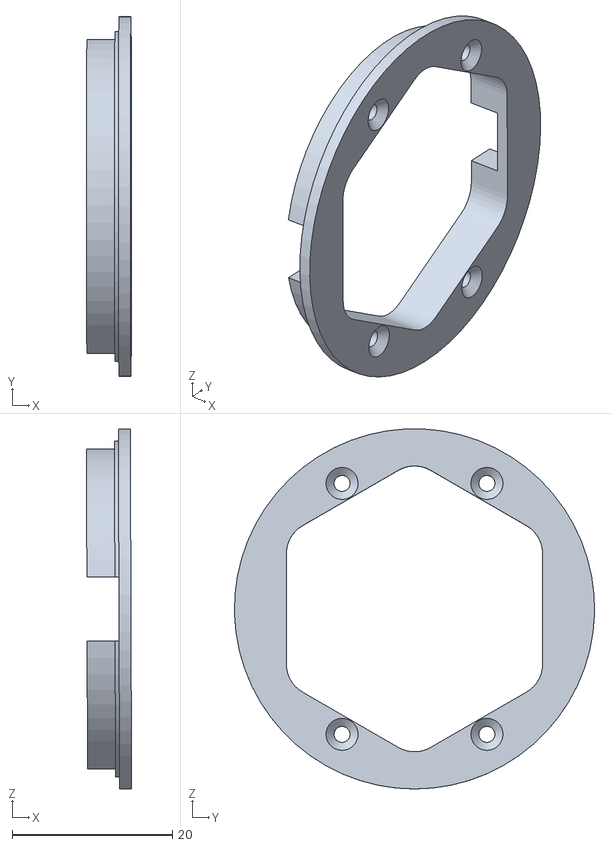
[picture p79: CAD file, 2020-09-06]
Teilnehmer/ultimate/V3 - 4Wheeler/Export/4-Wheeler - Rad-1 Rad-Nabe-2.STL
5.64 x 45.0 x 45.0
