ultimate/F-OR1/Teilnehmer/ultimate/V3 - 4Wheeler/Lager-Abstandsscheibe.SLDPRT

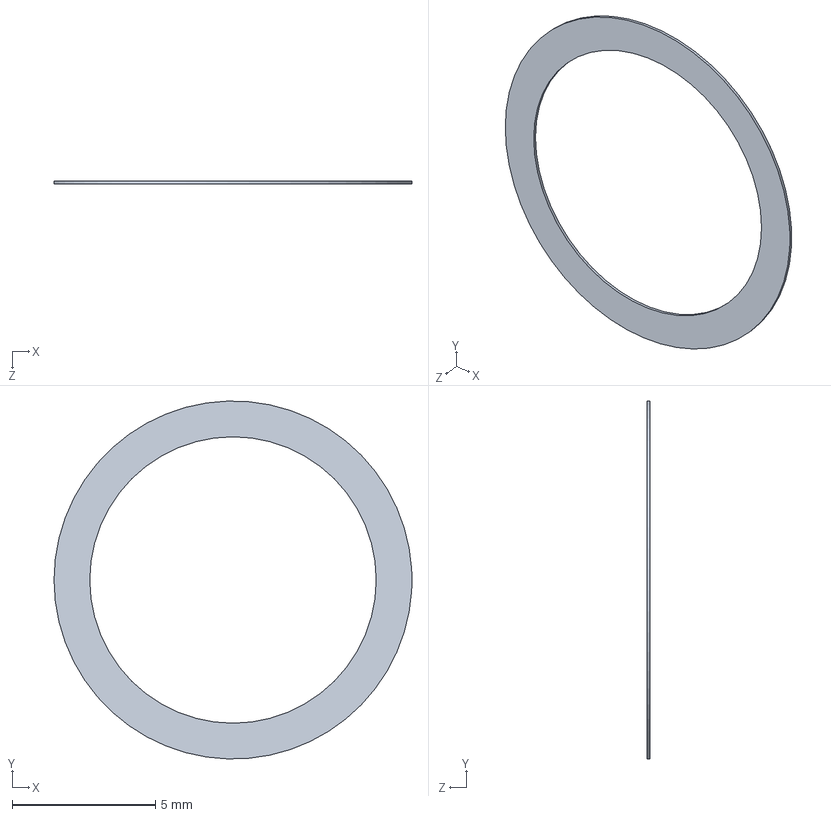
[picture p80: CAD file, 2019-10-27]
Teilnehmer/ultimate/V3 - 4Wheeler/Lager-Abstandsscheibe.SLDPRT
12.5 x 12.5 x 0.1 mm
