ultimate/F-OR1/Komponenten/Servo HK15138.SLDPRT

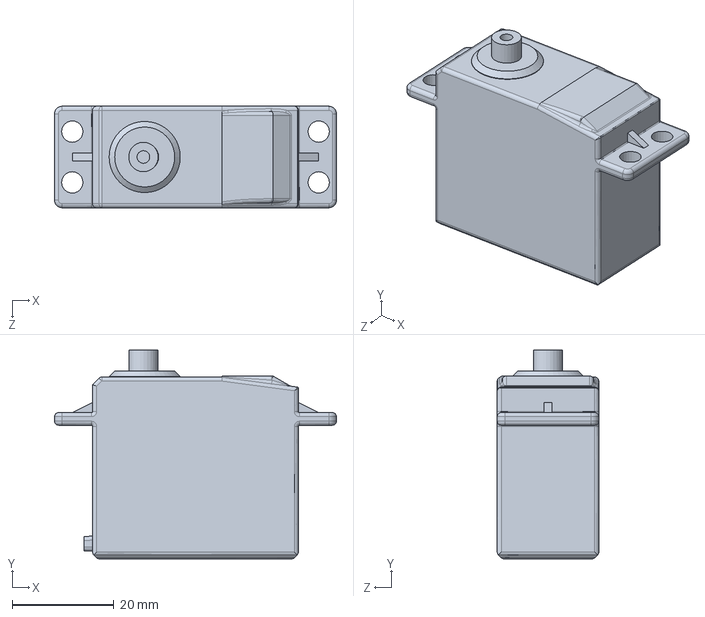
[picture p81: CAD file, 2019-10-27]
Komponenten/Servo HK15138.SLDPRT
55.5 x 41.1 x 20.0 mm
