ultimate/F-OR1/Komponenten/Step/Fahrtregler.stp

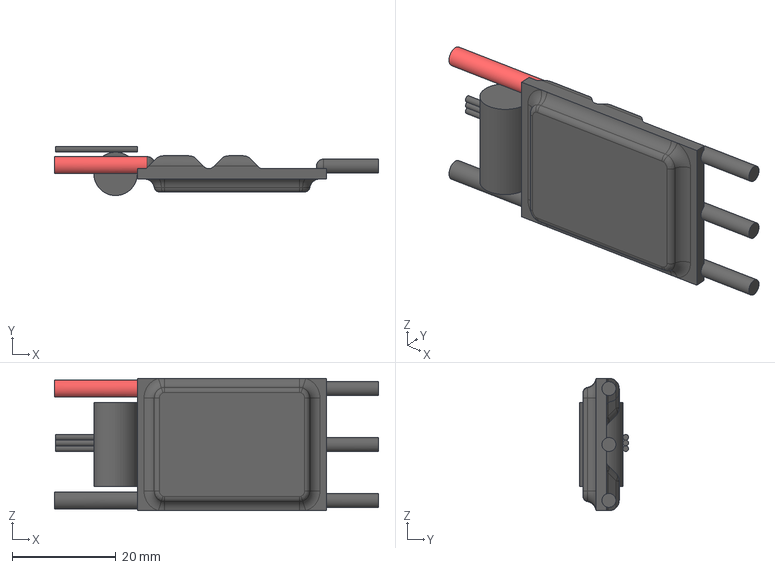
[picture p82: CAD file, 2014-05-16]
Komponenten/Step/Fahrtregler.stp
62.6 x 9.50 x 25.6 mm
