ultimate/F-OR1/Normteile/Step/Mädler 28104000.stp

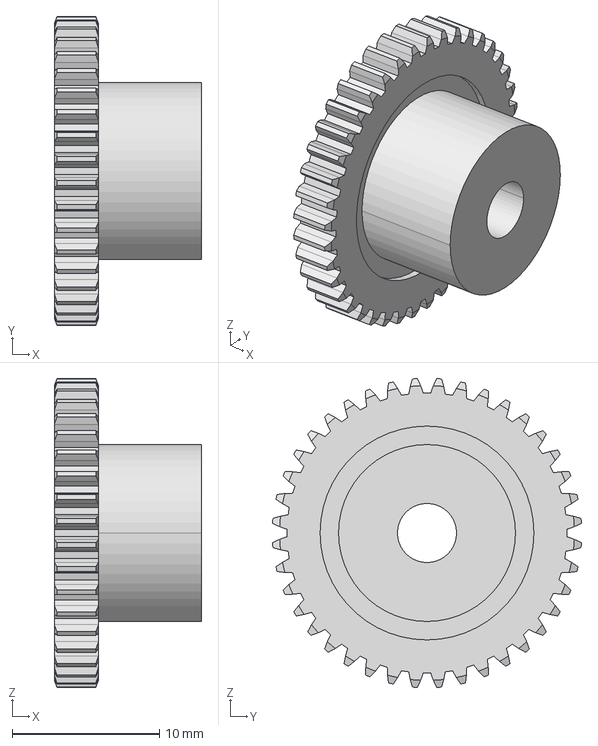
[picture p83: CAD file, 2019-10-27]
Normteile/Step/Mädler 28104000.stp
10.0 x 21.0 x 21.0 mm
