ultimate/F-OR1/Teilnehmer/ultimate/Test/Planetengetriebe Sonnenrad 0.5M.SLDPRT

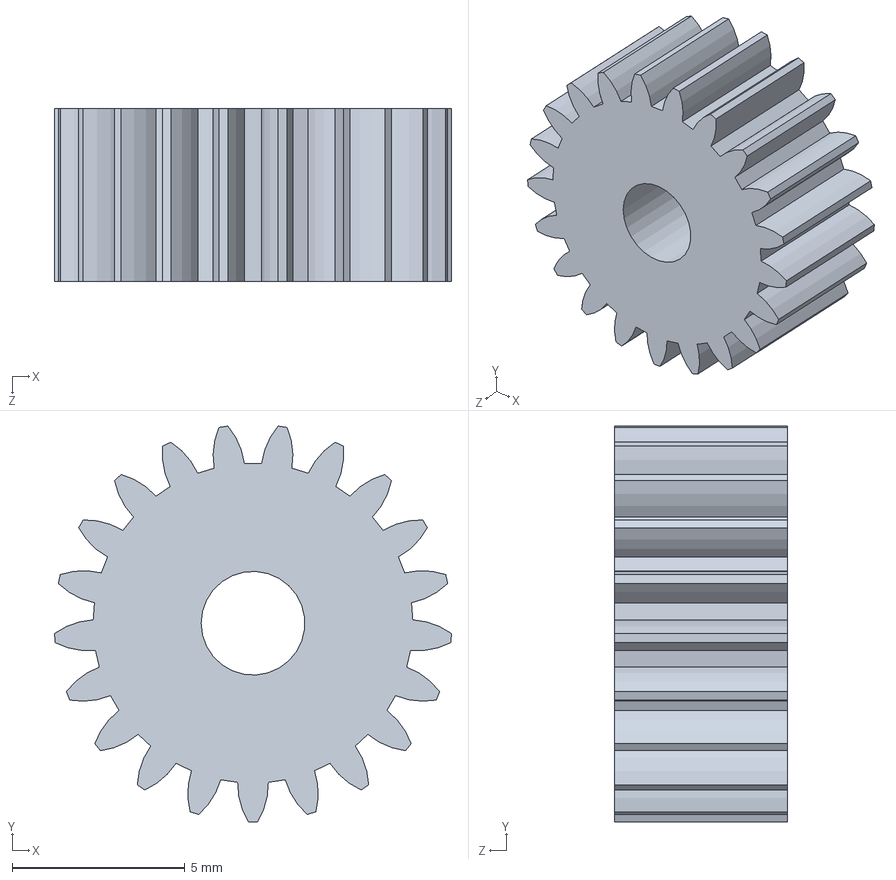
[picture p84: CAD file, 2019-10-27]
Teilnehmer/ultimate/Test/Planetengetriebe Sonnenrad 0.5M.SLDPRT
11.5 x 11.5 x 5.00 mm
