ultimate/F-OR1/Teilnehmer/ultimate/V0 - draft/draft_wheel.SLDPRT

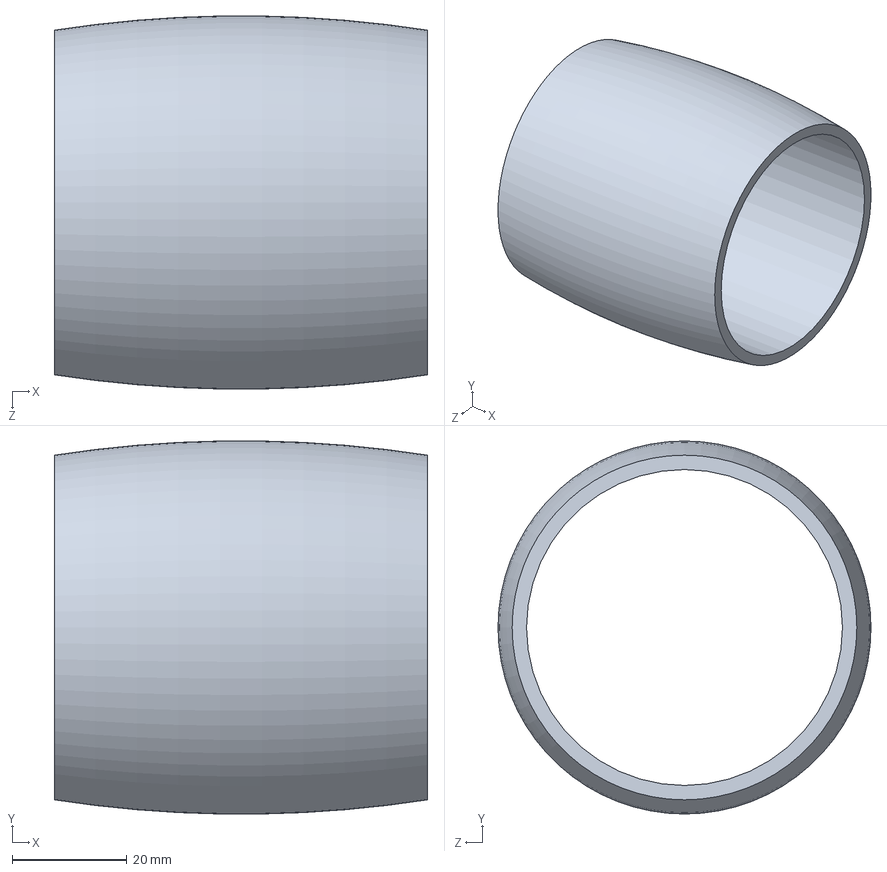
[picture p85: CAD file, 2019-10-27]
Teilnehmer/ultimate/V0 - draft/draft_wheel.SLDPRT
65.0 x 64.9 x 64.9 mm
