ultimate/F-OR1/Teilnehmer/ultimate/V1 - 3Wheeler/Druck/Rad-Hinten-Aufnahme.STL

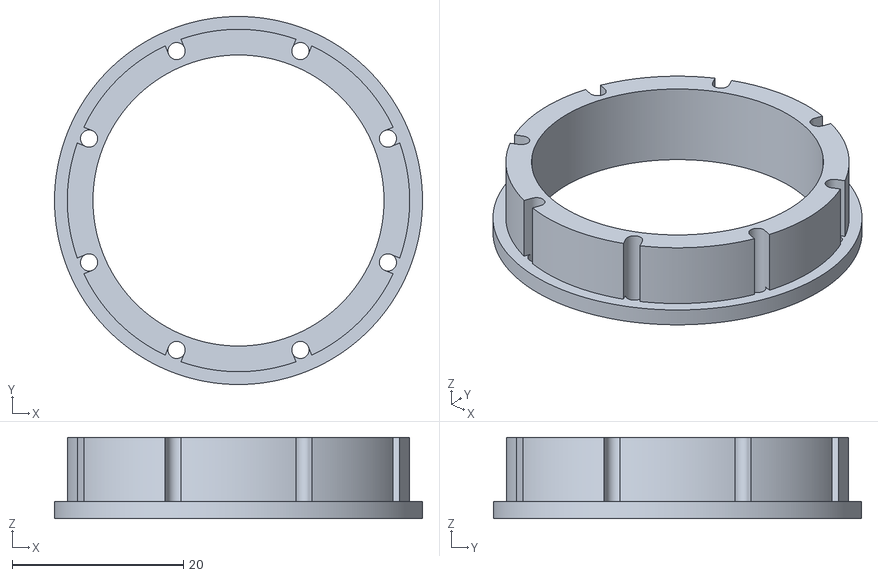
[picture p86: CAD file, 2019-10-27]
Teilnehmer/ultimate/V1 - 3Wheeler/Druck/Rad-Hinten-Aufnahme.STL
43.0 x 43.0 x 9.50
