ultimate/F-OR1/Teilnehmer/ultimate/V1 - 3Wheeler/Fertigung/Rahmen-Versteifung-Vorne.DXF

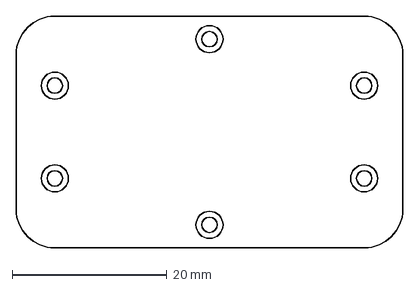
[picture p87: CAD file, 2019-10-27]
Teilnehmer/ultimate/V1 - 3Wheeler/Fertigung/Rahmen-Versteifung-Vorne.DXF
50.0 x 30.0 mm
