ultimate/F-OR1/Teilnehmer/ultimate/V1 - 3Wheeler/Rad-Vorne-Aufnahme.SLDPRT

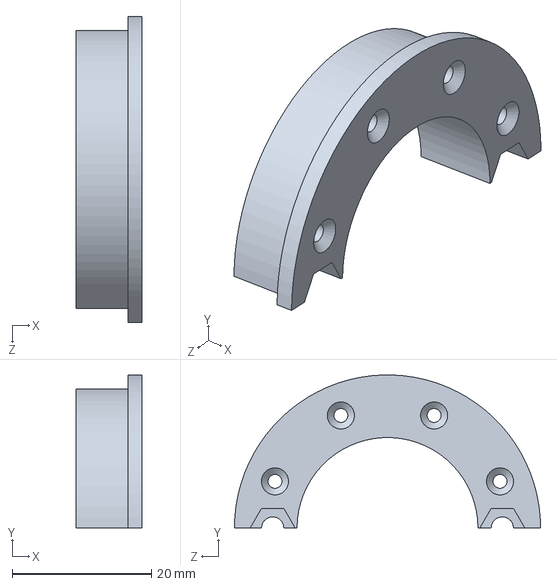
[picture p88: CAD file, 2019-10-27]
Teilnehmer/ultimate/V1 - 3Wheeler/Rad-Vorne-Aufnahme.SLDPRT
9.50 x 22.0 x 44.0 mm
