ultimate/F-OR1/Teilnehmer/ultimate/V2 - Lego/Servo-Horn-4er-modifiziert.SLDPRT

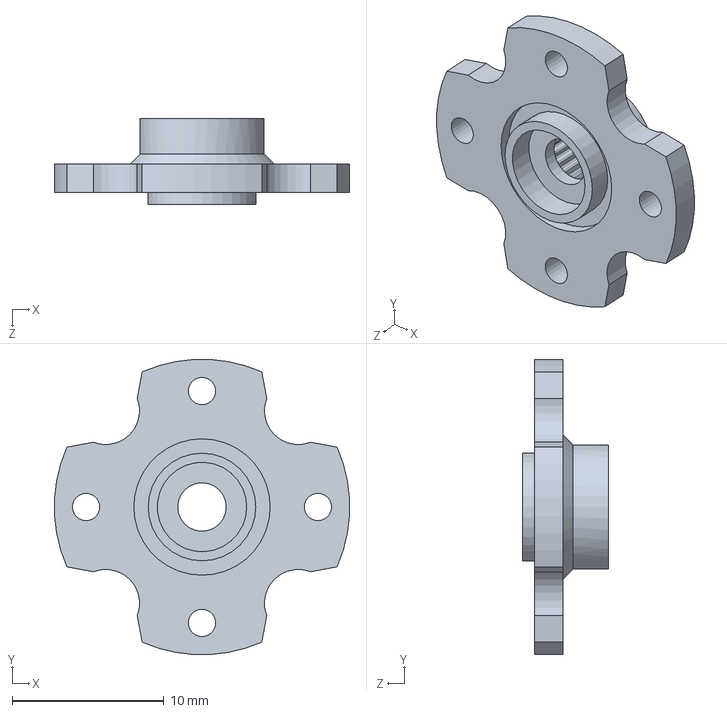
[picture p89: CAD file, 2019-10-27]
Teilnehmer/ultimate/V2 - Lego/Servo-Horn-4er-modifiziert.SLDPRT
19.5 x 19.5 x 5.70 mm
