ultimate/F-OR1/Teilnehmer/ultimate/V3 - 4Wheeler/Fertigung/Rahmen-Seite.DXF

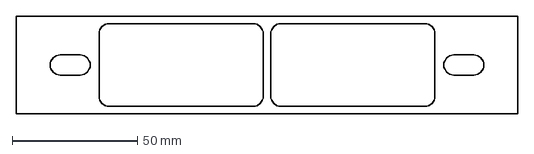
[picture p90: CAD file, 2019-10-27]
Teilnehmer/ultimate/V3 - 4Wheeler/Fertigung/Rahmen-Seite.DXF
200.0 x 39.0 mm
