ultimate/F-OR1/Komponenten/Kugel-Diff Hobbyking Mission-D Riemenrad.SLDPRT

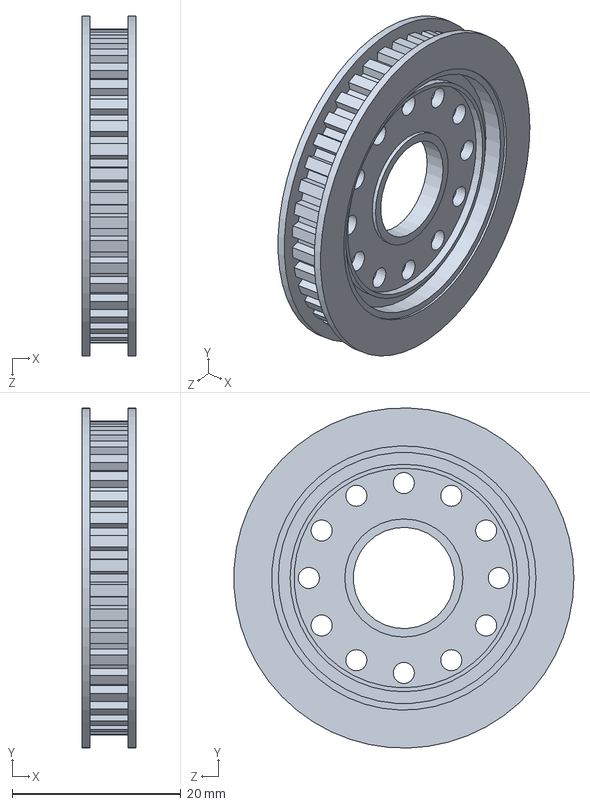
[picture p91: CAD file, 2019-10-27]
Komponenten/Kugel-Diff Hobbyking Mission-D Riemenrad.SLDPRT
6.40 x 40.3 x 40.3 mm
