ultimate/F-OR1/Komponenten/Step/Akku_Rhino1050.stp

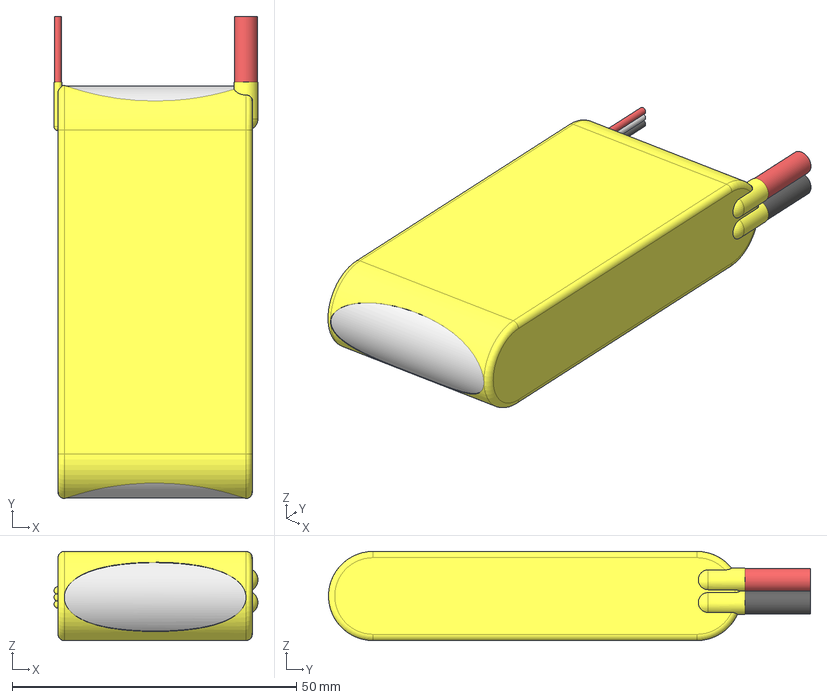
[picture p92: CAD file, 2014-05-16]
Komponenten/Step/Akku_Rhino1050.stp
35.9 x 84.8 x 15.7 mm
