ultimate/F-OR1/Normteile/Step/Mädler 28101900.stp

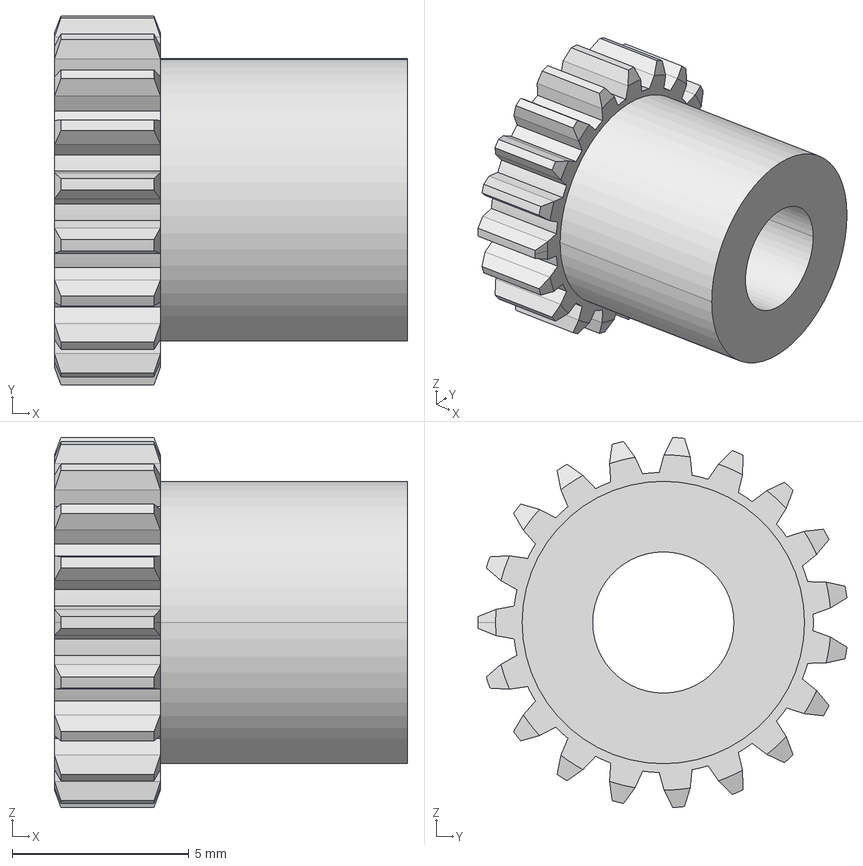
[picture p93: CAD file, 2019-10-27]
Normteile/Step/Mädler 28101900.stp
10.0 x 10.5 x 10.5 mm
