ultimate/F-OR1/Normteile/Zahnriemenrad T2.5 B6 ab Z20.SLDPRT

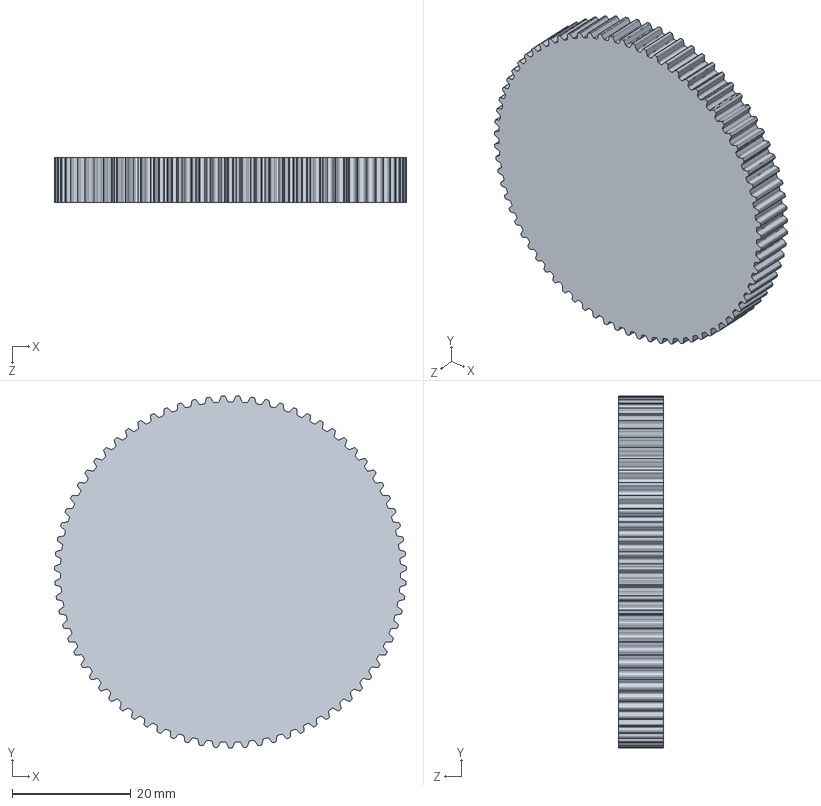
[picture p94: CAD file, 2019-10-27]
Normteile/Zahnriemenrad T2.5 B6 ab Z20.SLDPRT
59.2 x 59.2 x 7.50 mm
