ultimate/F-OR1/Teilnehmer/ultimate/V1 - 3Wheeler/Druck/Rad-Vorne-Innenkranz.STL

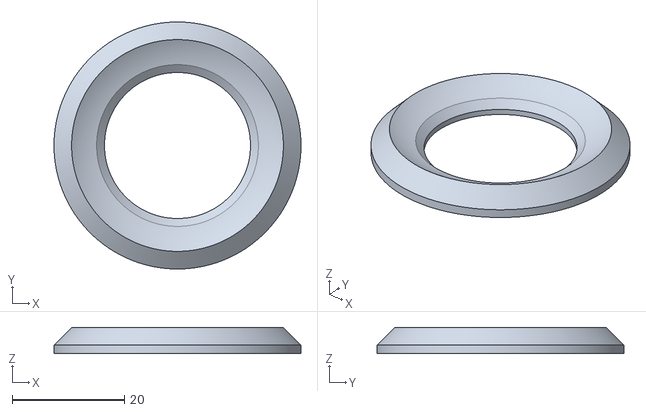
[picture p95: CAD file, 2019-10-27]
Teilnehmer/ultimate/V1 - 3Wheeler/Druck/Rad-Vorne-Innenkranz.STL
44.0 x 44.0 x 4.65
