ultimate/F-OR1/Teilnehmer/ultimate/V1 - 3Wheeler/Fertigung/Rahmen-Antrieb-Platine-Seite3.DXF

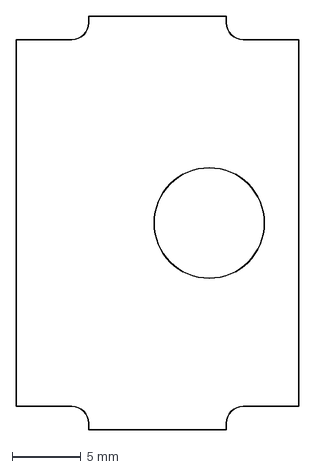
[picture p96: CAD file, 2019-10-27]
Teilnehmer/ultimate/V1 - 3Wheeler/Fertigung/Rahmen-Antrieb-Platine-Seite3.DXF
20.5 x 30.0 mm
