ultimate/F-OR1/Teilnehmer/ultimate/V1 - 3Wheeler/Rad-Hinten-Zahnkranz.SLDPRT

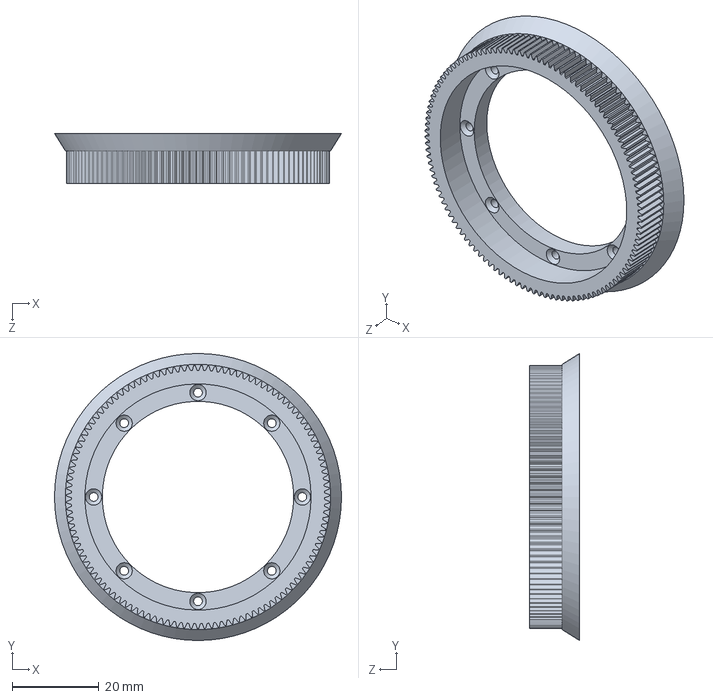
[picture p97: CAD file, 2019-10-27]
Teilnehmer/ultimate/V1 - 3Wheeler/Rad-Hinten-Zahnkranz.SLDPRT
66.0 x 66.0 x 11.5 mm
