ultimate/F-OR1/Teilnehmer/ultimate/V3 - 4Wheeler/Export/4-Wheeler - Antrieb-1 Antrieb-Spanner-2 Antrieb-Spanner-Lagerhülse-3.STL

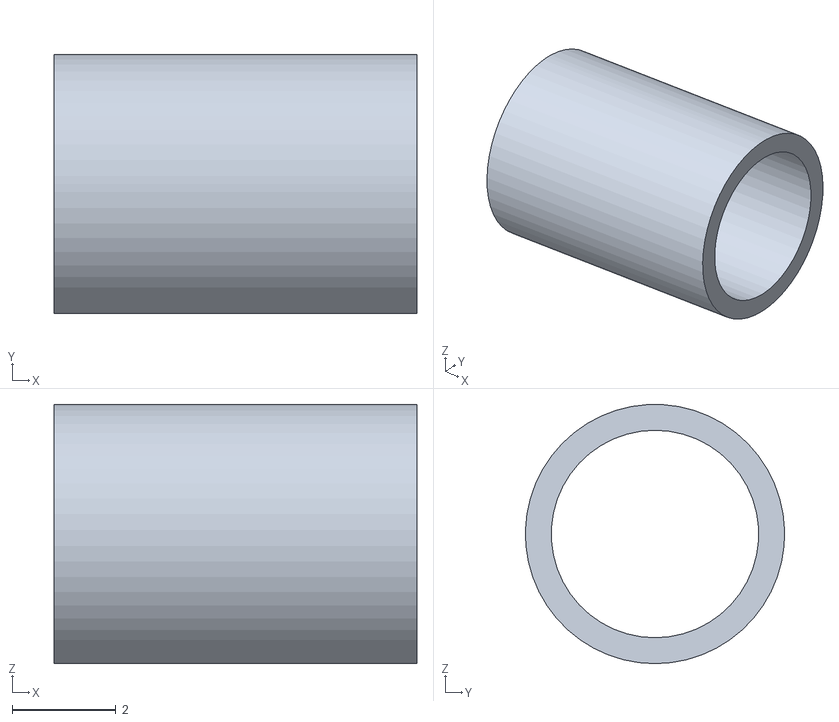
[picture p98: CAD file, 2020-09-06]
Teilnehmer/ultimate/V3 - 4Wheeler/Export/4-Wheeler - Antrieb-1 Antrieb-Spanner-2 Antrieb-Spanner-Lagerhülse-3.STL
7.00 x 5.00 x 5.00
