ultimate/F-OR1/Teilnehmer/ultimate/V3 - 4Wheeler/Fertigung/Rahmen-Vorne.DXF

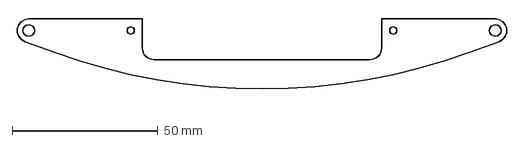
[picture p99: CAD file, 2019-10-27]
Teilnehmer/ultimate/V3 - 4Wheeler/Fertigung/Rahmen-Vorne.DXF
168.6 x 28.2 mm
