ultimate/F-OR1/Komponenten/Step/Motor_B20-30-24S-FIN.stp

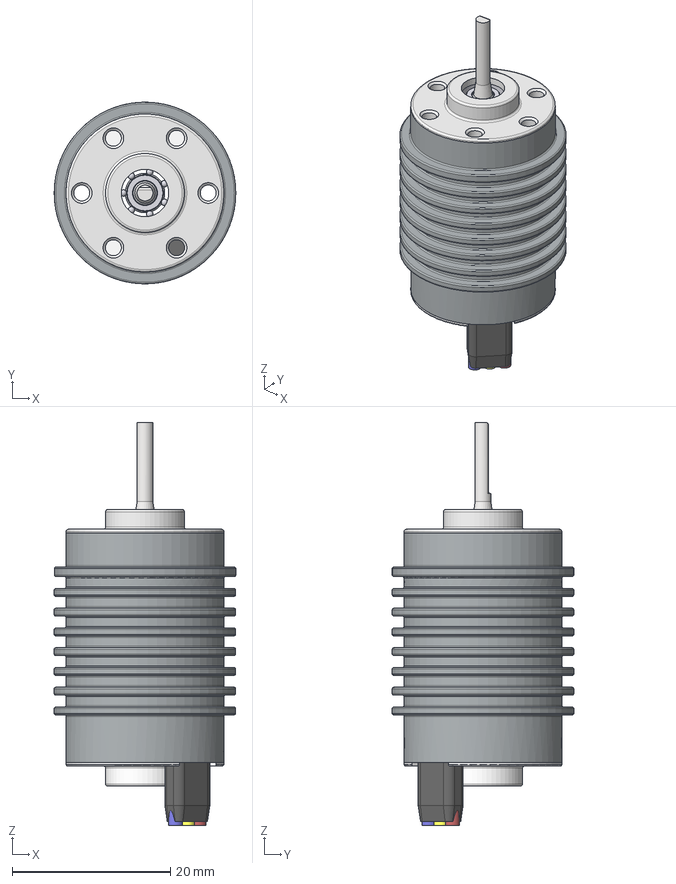
[picture p100: CAD file, 2014-05-16]
Komponenten/Step/Motor_B20-30-24S-FIN.stp
23.0 x 23.0 x 51.0 mm
Motorgehäuse
MotorflanschHinten
Bearing GB/T 5800-2003 639/3 x 2
MotorflanschVorne
MotorRotorwelle
