ultimate/F-OR1/Teilnehmer/ultimate/Test/Kardan-1.SLDPRT

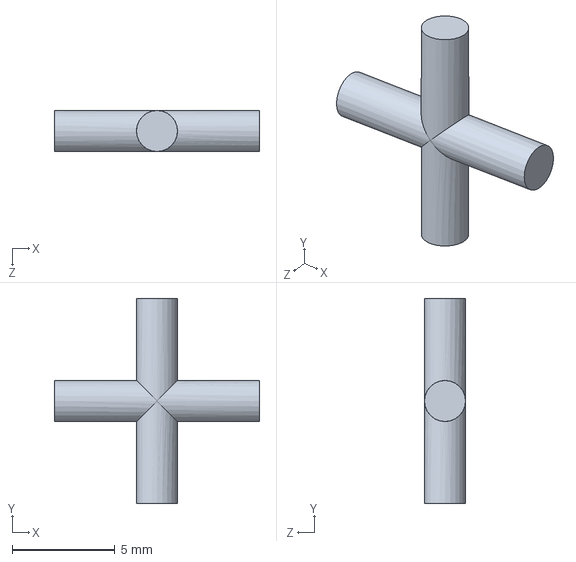
[picture p101: CAD file, 2019-10-27]
Teilnehmer/ultimate/Test/Kardan-1.SLDPRT
10.0 x 10.0 x 2.00 mm
