ultimate/F-OR1/Teilnehmer/ultimate/V1 - 3Wheeler/Druck/Zahnriemenrad T2.5 B6 Z13 Di5.STL

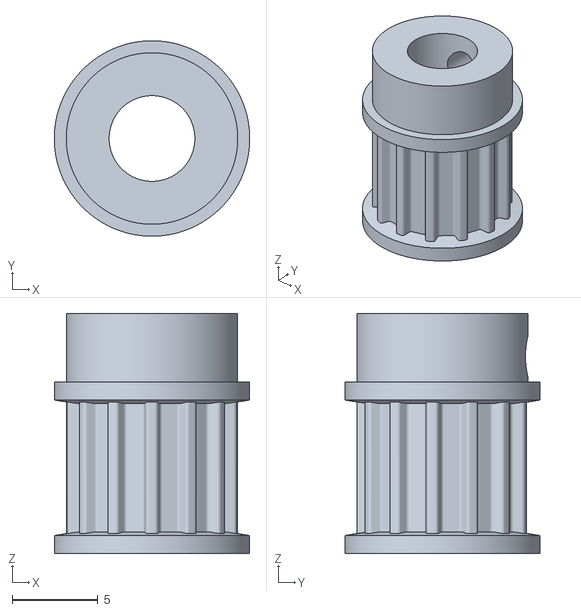
[picture p102: CAD file, 2019-10-27]
Teilnehmer/ultimate/V1 - 3Wheeler/Druck/Zahnriemenrad T2.5 B6 Z13 Di5.STL
11.4 x 11.4 x 14.0
