ultimate/F-OR1/Teilnehmer/ultimate/V1 - 3Wheeler/Fertigung/Rahmen-Antrieb-Platine-Anschluss2.DXF

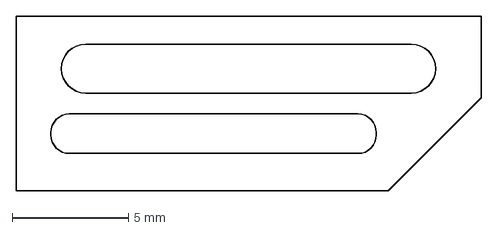
[picture p103: CAD file, 2019-10-27]
Teilnehmer/ultimate/V1 - 3Wheeler/Fertigung/Rahmen-Antrieb-Platine-Anschluss2.DXF
20.0 x 7.50 mm
