ultimate/F-OR1/Teilnehmer/ultimate/V3 - 4Wheeler/Antrieb-Spanner-Rolle.SLDPRT

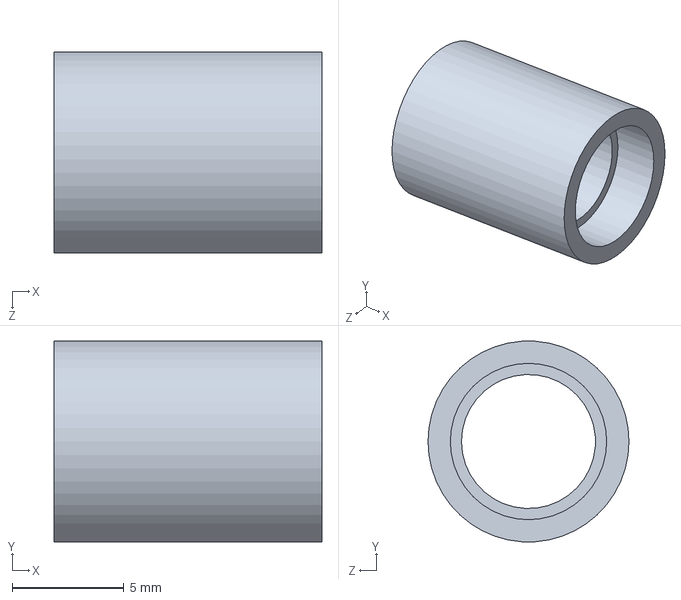
[picture p104: CAD file, 2019-10-27]
Teilnehmer/ultimate/V3 - 4Wheeler/Antrieb-Spanner-Rolle.SLDPRT
12.0 x 8.98 x 9.00 mm
