ultimate/F-OR1/Teilnehmer/ultimate/V3 - 4Wheeler/Export/4-Wheeler - Antrieb-1 Motor_B20-30-24S-FIN-1 Motor_B20-30-24S-FIN-Lager-2.STL

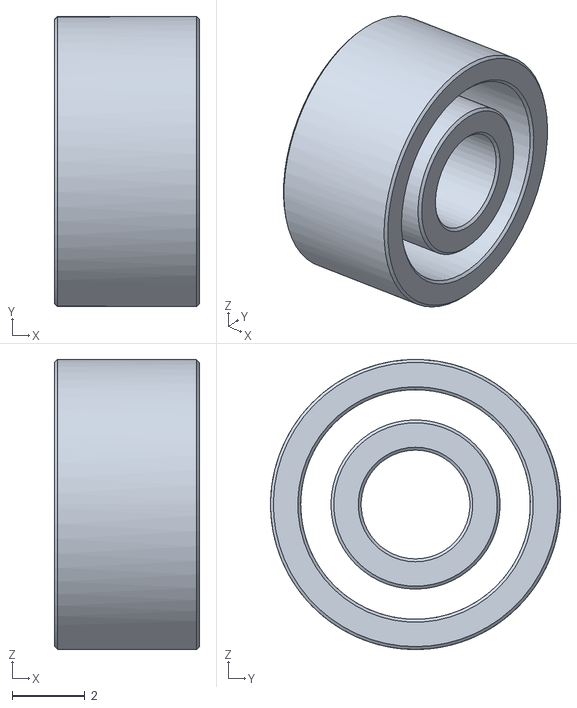
[picture p105: CAD file, 2020-09-06]
Teilnehmer/ultimate/V3 - 4Wheeler/Export/4-Wheeler - Antrieb-1 Motor_B20-30-24S-FIN-1 Motor_B20-30-24S-FIN-Lager-2.STL
4.00 x 8.00 x 8.00
