ultimate/F-OR1/Teilnehmer/ultimate/V3 - 4Wheeler/Fertigung/Rad-Lagersitz.DXF

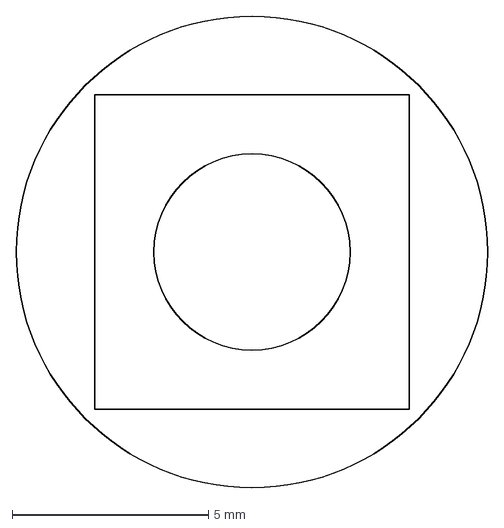
[picture p106: CAD file, 2019-10-27]
Teilnehmer/ultimate/V3 - 4Wheeler/Fertigung/Rad-Lagersitz.DXF
12.0 x 12.0 mm
