ultimate/F-OR1/Komponenten/Riemenrad Hobbyking Mission-D.SLDPRT

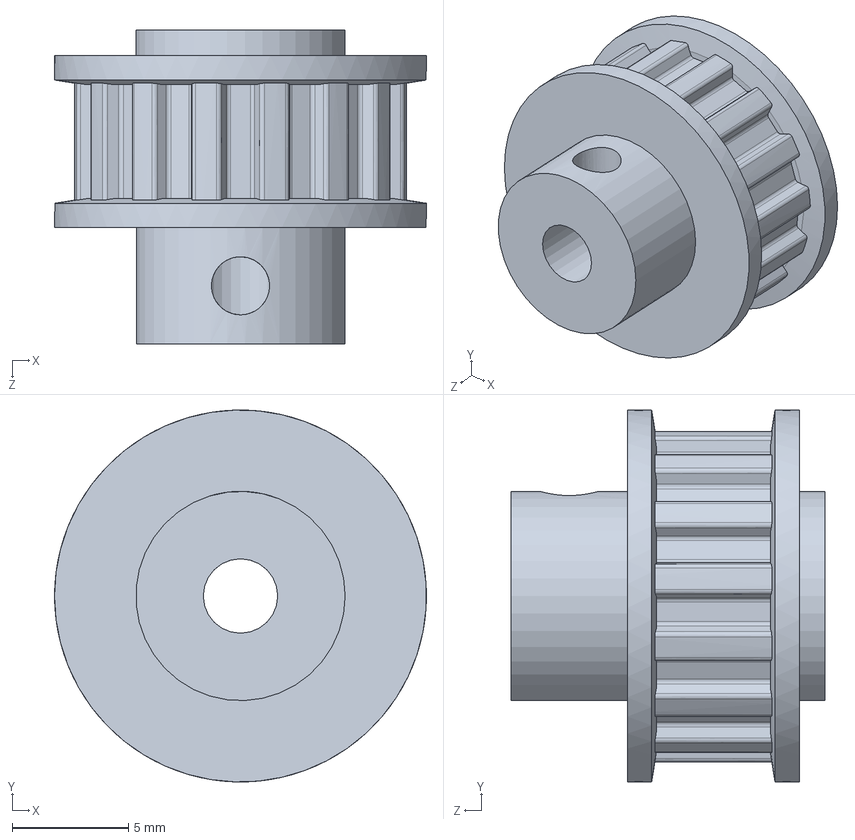
[picture p107: CAD file, 2019-10-27]
Komponenten/Riemenrad Hobbyking Mission-D.SLDPRT
16.0 x 16.0 x 13.5 mm
