ultimate/F-OR1/Komponenten/Step/Empfaenger_TR6A.stp

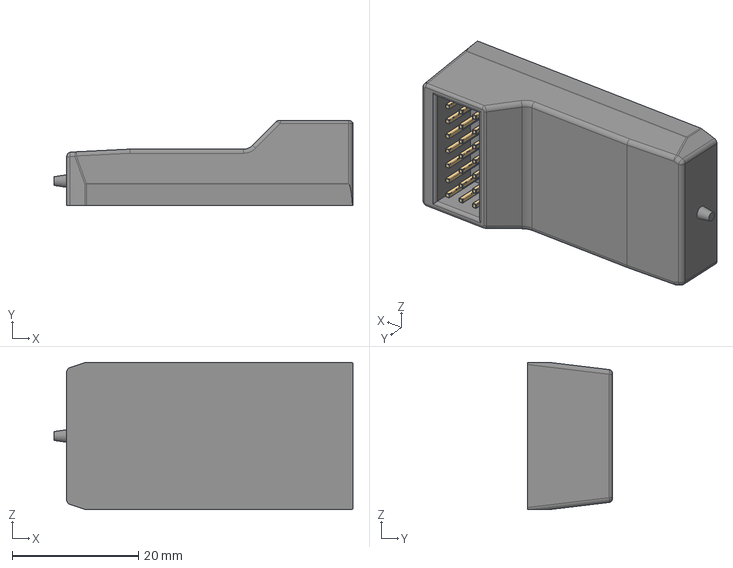
[picture p108: CAD file, 2014-05-16]
Komponenten/Step/Empfaenger_TR6A.stp
47.3 x 13.4 x 23.3 mm
