ultimate/F-OR1/Normteile/Zahnrad 0.5M 15T.SLDPRT

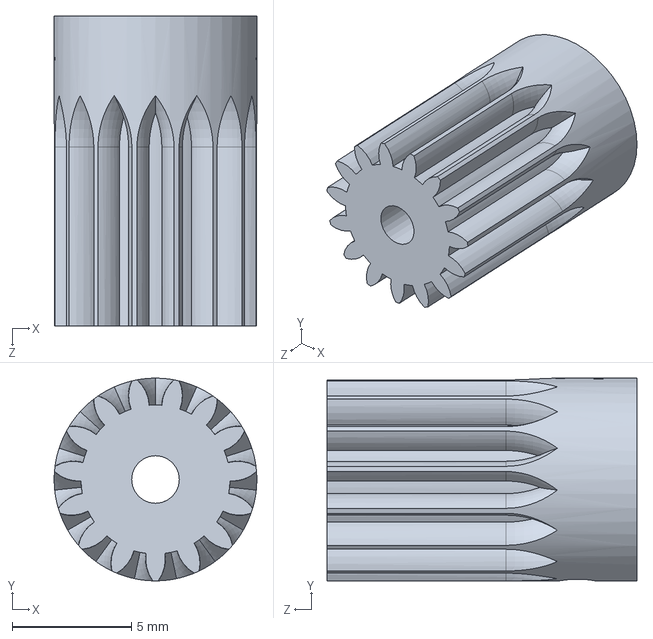
[picture p109: CAD file, 2019-10-27]
Normteile/Zahnrad 0.5M 15T.SLDPRT
8.50 x 8.50 x 13.0 mm
