ultimate/F-OR1/Teilnehmer/ultimate/Test/Planetengetriebe Hohlrad 0.5M.SLDPRT

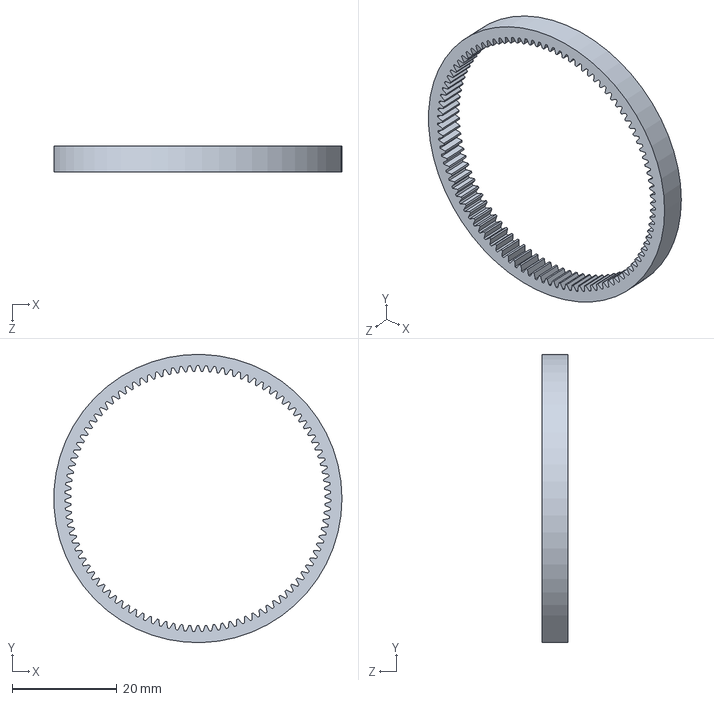
[picture p110: CAD file, 2019-10-27]
Teilnehmer/ultimate/Test/Planetengetriebe Hohlrad 0.5M.SLDPRT
55.0 x 55.0 x 5.00 mm
