ultimate/F-OR1/Teilnehmer/ultimate/V1 - 3Wheeler/Druck/Rad-Vorne-Korpus A1.STL

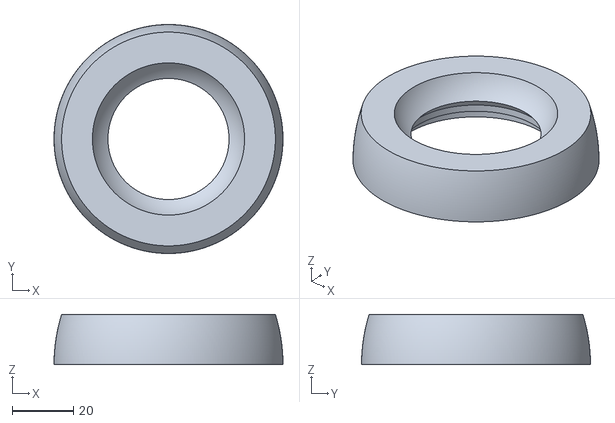
[picture p111: CAD file, 2019-10-27]
Teilnehmer/ultimate/V1 - 3Wheeler/Druck/Rad-Vorne-Korpus A1.STL
75.0 x 75.0 x 16.5
