ultimate/F-OR1/Teilnehmer/ultimate/V1 - 3Wheeler/Rahmen-Servo.SLDPRT

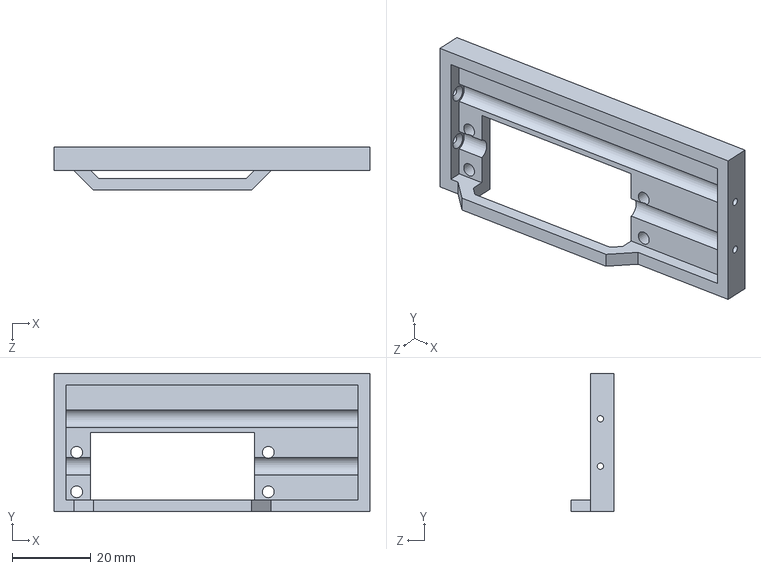
[picture p113: CAD file, 2019-10-27]
Teilnehmer/ultimate/V1 - 3Wheeler/Rahmen-Servo.SLDPRT
80.0 x 35.0 x 11.0 mm
