ultimate/F-OR1/Teilnehmer/ultimate/V2 - Lego/Aufnahme-Lüfter.SLDPRT

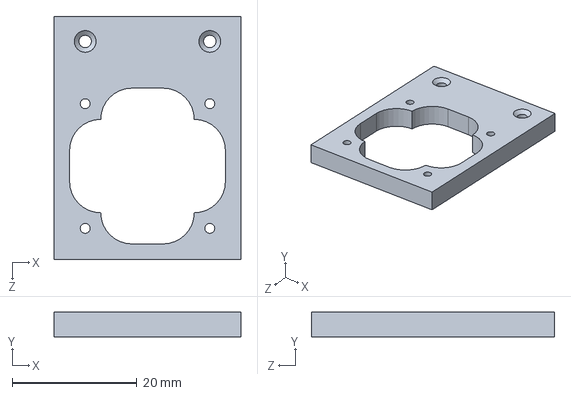
[picture p114: CAD file, 2019-10-27]
Teilnehmer/ultimate/V2 - Lego/Aufnahme-Lüfter.SLDPRT
30.0 x 4.00 x 39.0 mm
