ultimate/F-OR1/Teilnehmer/ultimate/V3 - 4Wheeler/Export/4-Wheeler - Lenkstange-1 Gelenkbolzen-5.STL

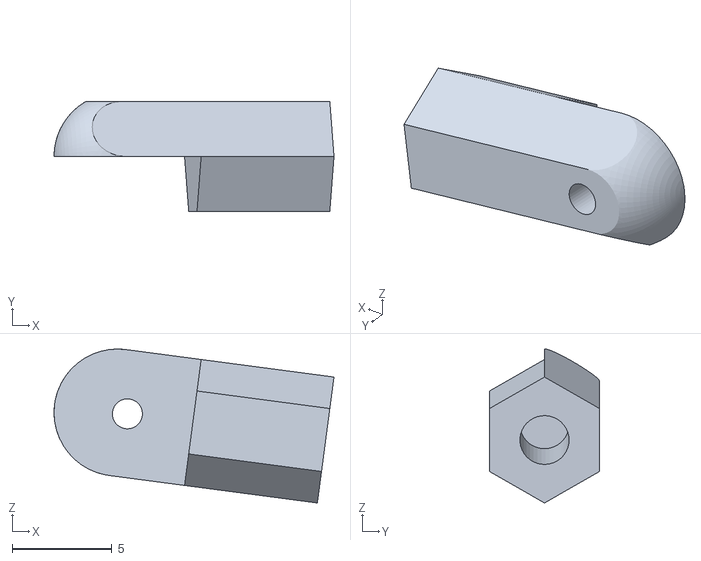
[picture p115: CAD file, 2020-09-06]
Teilnehmer/ultimate/V3 - 4Wheeler/Export/4-Wheeler - Lenkstange-1 Gelenkbolzen-5.STL
14.0 x 5.50 x 7.70
