ultimate/F-OR1/Teilnehmer/ultimate/V3 - 4Wheeler/Fertigung/Rahmen-Hinten.DXF

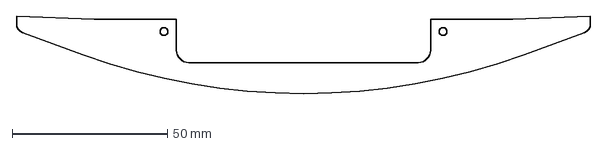
[picture p116: CAD file, 2019-10-27]
Teilnehmer/ultimate/V3 - 4Wheeler/Fertigung/Rahmen-Hinten.DXF
185.2 x 29.1 mm
