ultimate/F-OR1/Teilnehmer/ultimate/V3 - 4Wheeler/Rad-Nabe.SLDPRT

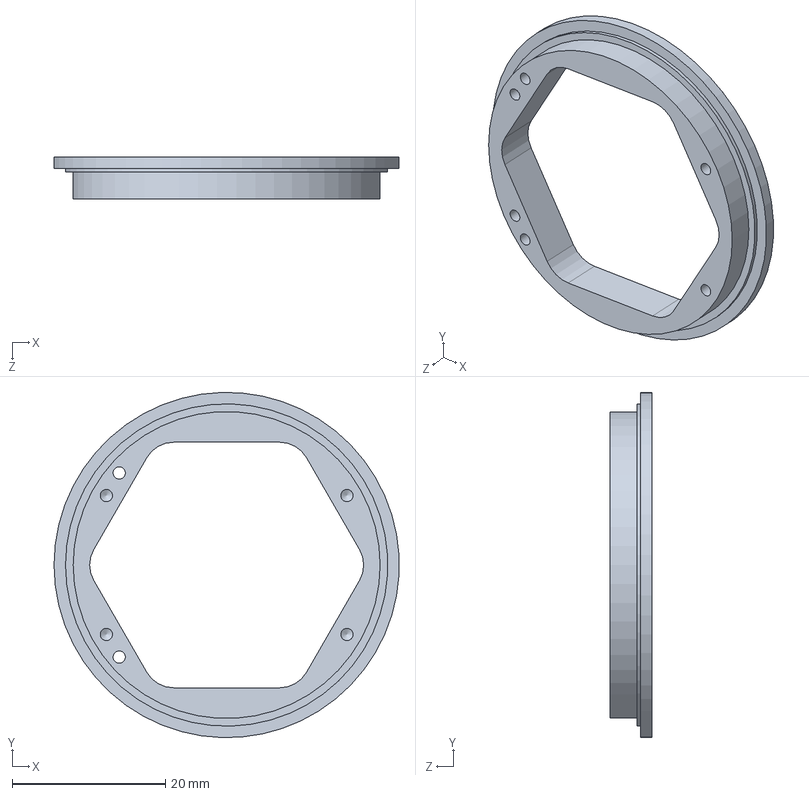
[picture p117: CAD file, 2019-10-27]
Teilnehmer/ultimate/V3 - 4Wheeler/Rad-Nabe.SLDPRT
45.0 x 45.0 x 5.50 mm
