ultimate/F-OR1/Komponenten/Step/Empfaenger_GT2.stp

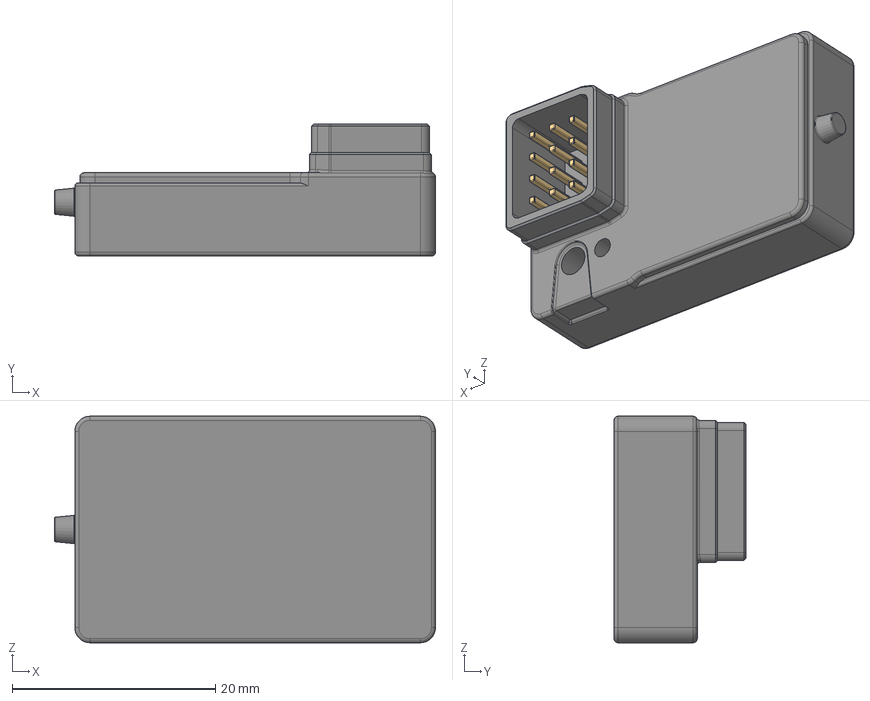
[picture p118: CAD file, 2014-05-16]
Komponenten/Step/Empfaenger_GT2.stp
37.5 x 13.0 x 22.3 mm
