ultimate/F-OR1/Normteile/DIN - Spur gear 0.5M 71T 20PA 5FW ---S71A75H50L3.0N.sldprt

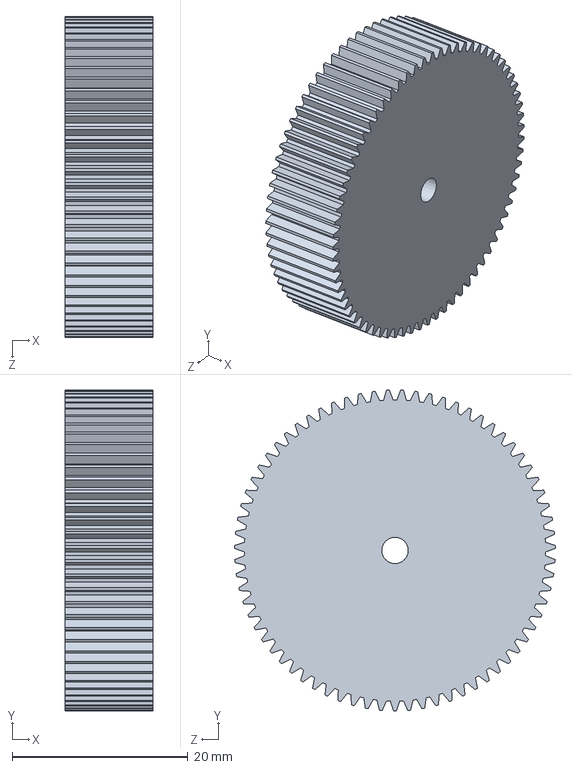
[picture p119: CAD file, 2019-10-27]
Normteile/DIN - Spur gear 0.5M 71T 20PA 5FW ---S71A75H50L3.0N.sldprt
10.0 x 36.5 x 36.5 mm
