ultimate/F-OR1/Teilnehmer/ultimate/V1 - 3Wheeler/Druck/Rahmen-Antrieb.STL

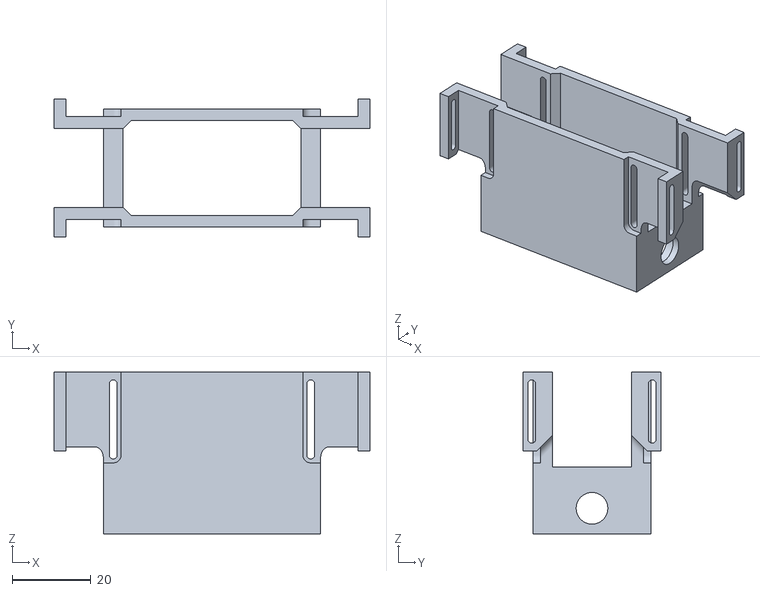
[picture p120: CAD file, 2019-10-27]
Teilnehmer/ultimate/V1 - 3Wheeler/Druck/Rahmen-Antrieb.STL
80.0 x 35.0 x 41.0
