ultimate/F-OR1/Teilnehmer/ultimate/V3 - 4Wheeler/Export/4-Wheeler - Rad-2 O-Ring-2.STL

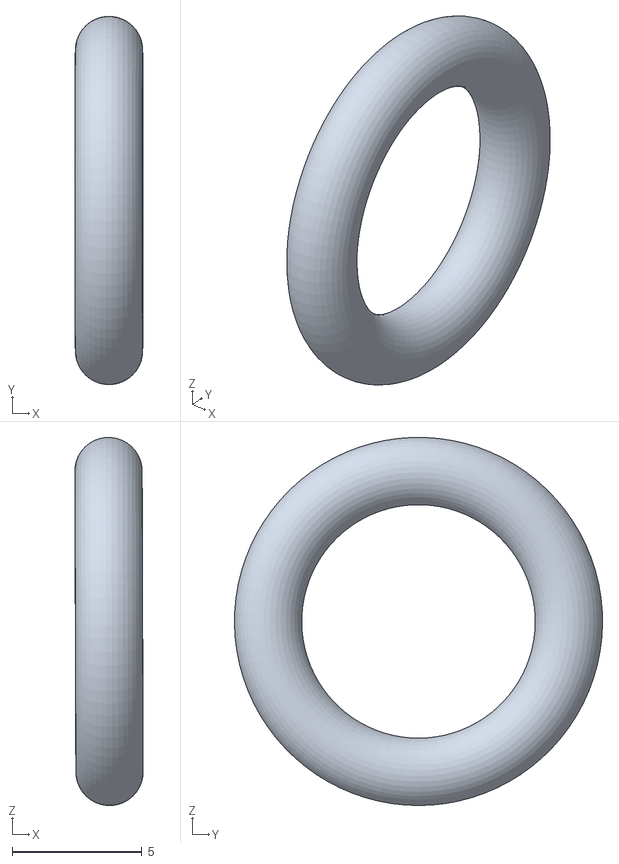
[picture p122: CAD file, 2020-09-06]
Teilnehmer/ultimate/V3 - 4Wheeler/Export/4-Wheeler - Rad-2 O-Ring-2.STL
2.64 x 14.2 x 14.2
