ultimate/F-OR1/Teilnehmer/ultimate/V3 - 4Wheeler/Fertigung/Rad-Adapter-Lenkung.STL

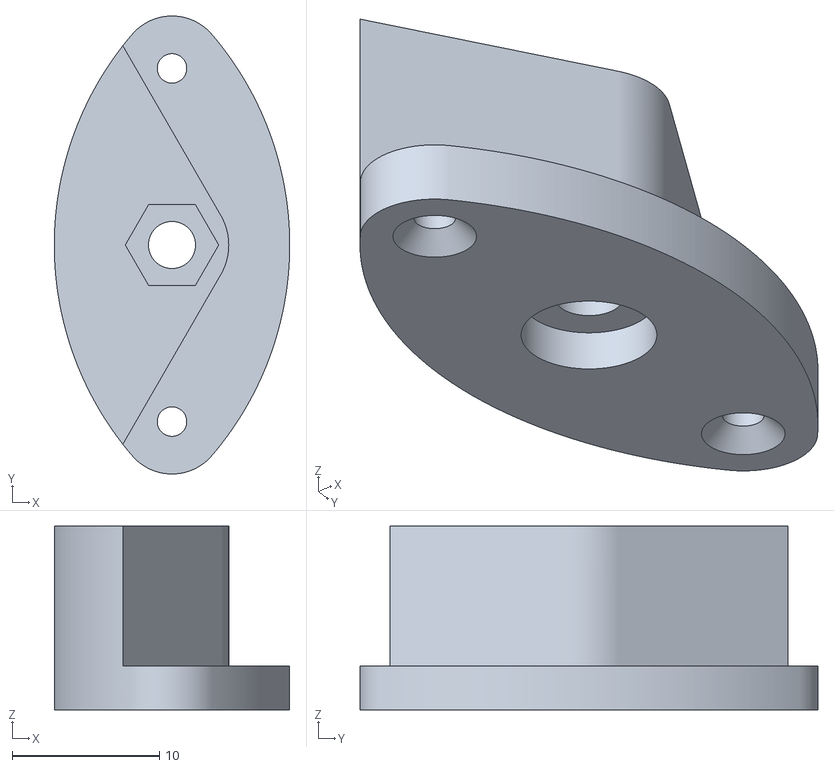
[picture p123: CAD file, 2019-10-27]
Teilnehmer/ultimate/V3 - 4Wheeler/Fertigung/Rad-Adapter-Lenkung.STL
16.0 x 31.1 x 12.5
