ultimate/F-OR1/Komponenten/Kugel-Diff Hobbyking Mission-D Laufscheibe.SLDPRT

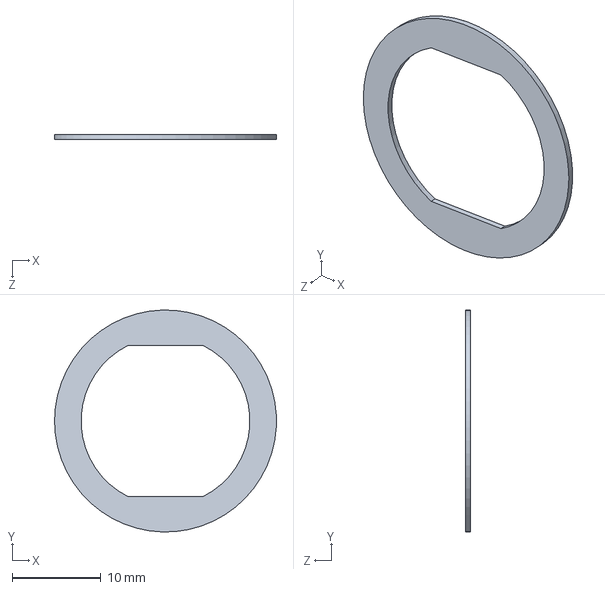
[picture p124: CAD file, 2019-10-27]
Komponenten/Kugel-Diff Hobbyking Mission-D Laufscheibe.SLDPRT
25.0 x 25.0 x 0.6 mm
