ultimate/F-OR1/Normteile/Kugellager - MR74.SLDPRT

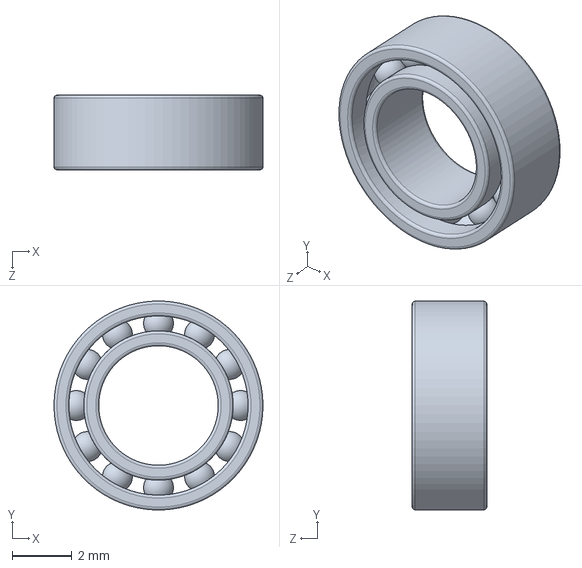
[picture p125: CAD file, 2019-10-27]
Normteile/Kugellager - MR74.SLDPRT
7.00 x 6.99 x 2.50 mm
