ultimate/F-OR1/Teilnehmer/ultimate/Test/Kardan-2.SLDPRT

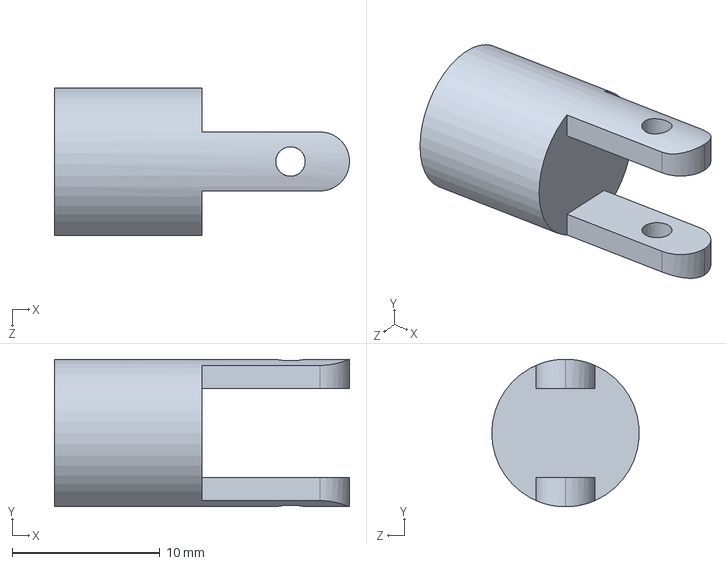
[picture p126: CAD file, 2019-10-27]
Teilnehmer/ultimate/Test/Kardan-2.SLDPRT
20.0 x 10.0 x 10.0 mm
