ultimate/F-OR1/Teilnehmer/ultimate/V2 - Lego/Fixier-Block.SLDPRT

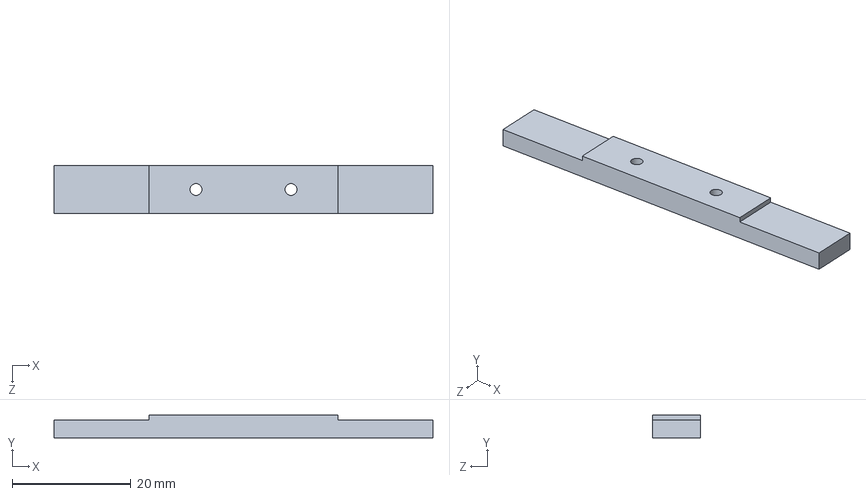
[picture p128: CAD file, 2019-10-27]
Teilnehmer/ultimate/V2 - Lego/Fixier-Block.SLDPRT
63.8 x 3.80 x 8.00 mm
