ultimate/F-OR1/Teilnehmer/ultimate/V3 - 4Wheeler/Export/4-Wheeler - Antrieb-1 Antrieb-Lagerbock-5.STL

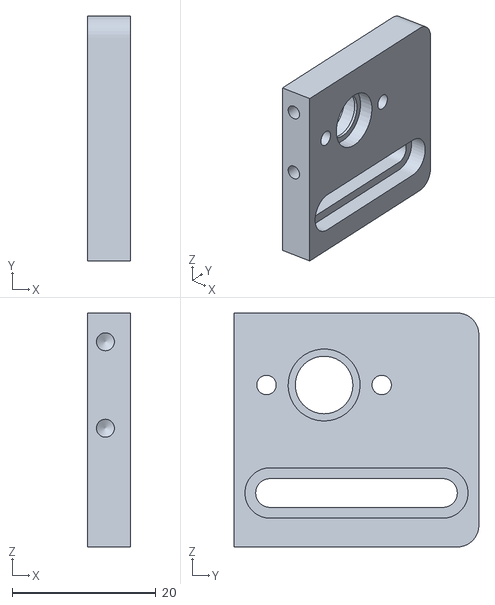
[picture p129: CAD file, 2020-09-06]
Teilnehmer/ultimate/V3 - 4Wheeler/Export/4-Wheeler - Antrieb-1 Antrieb-Lagerbock-5.STL
6.00 x 34.0 x 32.5
