ultimate/F-OR1/Teilnehmer/ultimate/V3 - 4Wheeler/Rahmen-Vorne.SLDPRT

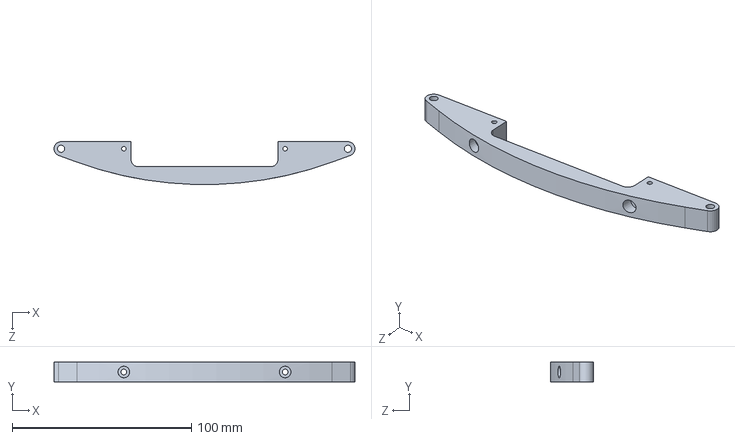
[picture p130: CAD file, 2019-10-27]
Teilnehmer/ultimate/V3 - 4Wheeler/Rahmen-Vorne.SLDPRT
168.0 x 11.0 x 23.9 mm
