ultimate/F-OR1/Komponenten/Kugel-Diff Hobbyking Mission-D Achse1.SLDPRT

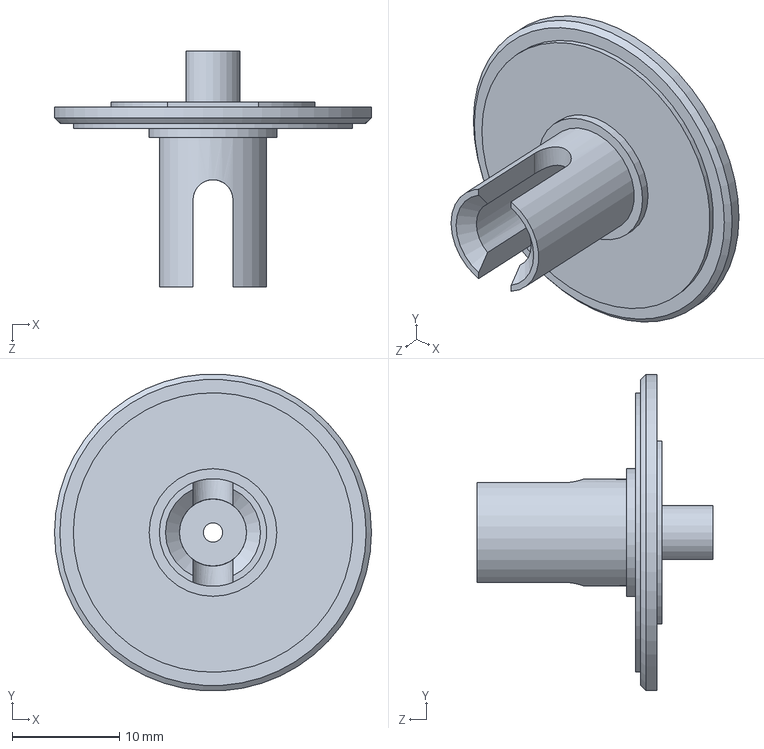
[picture p131: CAD file, 2019-10-27]
Komponenten/Kugel-Diff Hobbyking Mission-D Achse1.SLDPRT
29.5 x 29.4 x 22.0 mm
