ultimate/F-OR1/Normteile/DIN - Spur gear 0.5M 17T 20PA 5FW ---S17A75H50L2N.sldprt

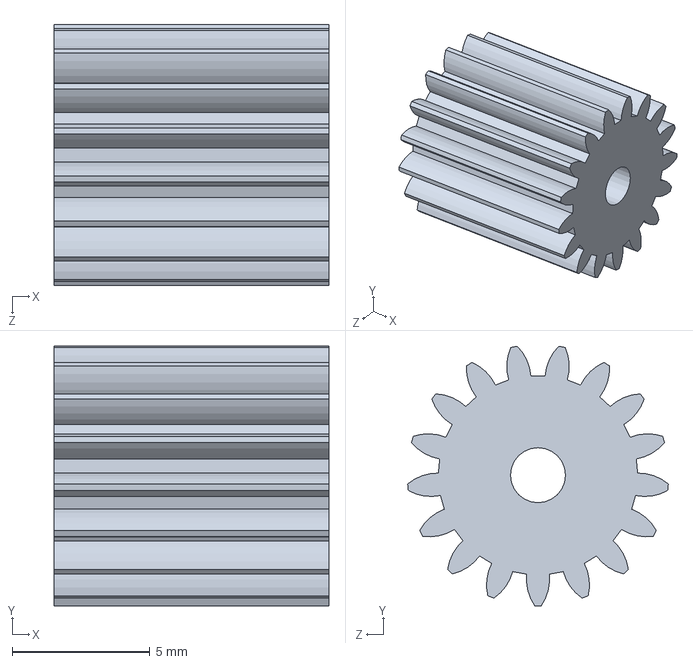
[picture p132: CAD file, 2019-10-27]
Normteile/DIN - Spur gear 0.5M 17T 20PA 5FW ---S17A75H50L2N.sldprt
10.0 x 9.44 x 9.48 mm
