ultimate/F-OR1/Teilnehmer/ultimate/Test/Kardan-Block.SLDPRT

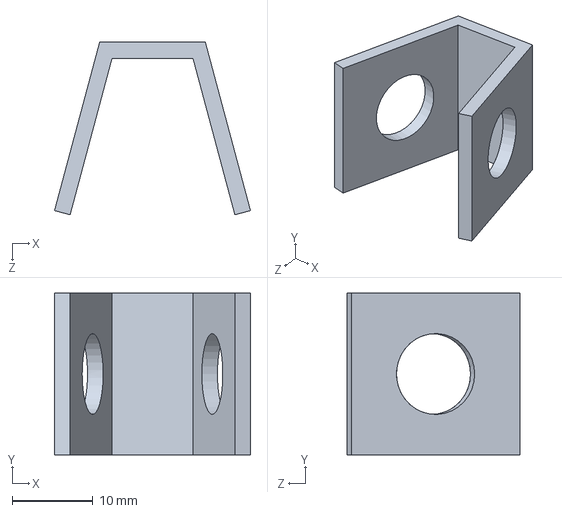
[picture p133: CAD file, 2019-10-27]
Teilnehmer/ultimate/Test/Kardan-Block.SLDPRT
24.2 x 20.0 x 21.3 mm
