ultimate/F-OR1/Teilnehmer/ultimate/V1 - 3Wheeler/Antrieb-B-Passhülse.SLDPRT

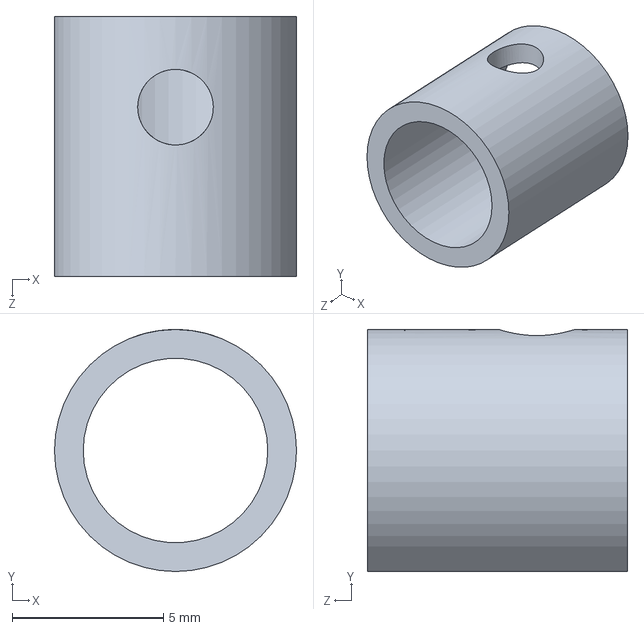
[picture p134: CAD file, 2019-10-27]
Teilnehmer/ultimate/V1 - 3Wheeler/Antrieb-B-Passhülse.SLDPRT
8.00 x 8.00 x 8.60 mm
