ultimate/F-OR1/Teilnehmer/ultimate/V1 - 3Wheeler/Druck/Lenk-Aufsatz.STL

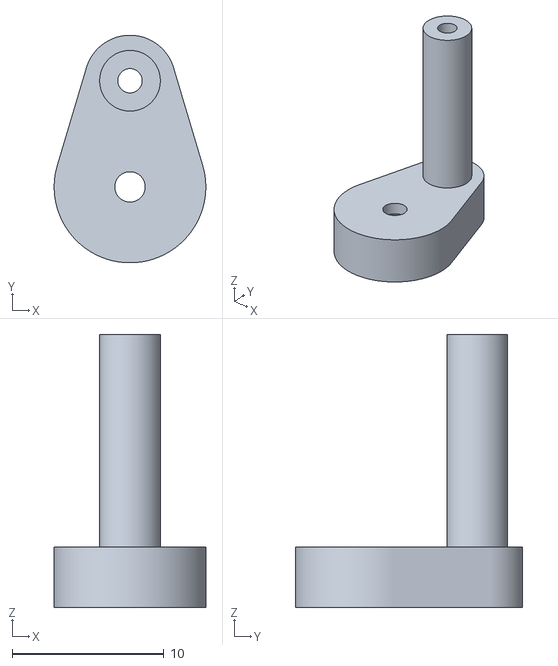
[picture p135: CAD file, 2019-10-27]
Teilnehmer/ultimate/V1 - 3Wheeler/Druck/Lenk-Aufsatz.STL
10.00 x 15.0 x 18.0
