ultimate/F-OR1/Teilnehmer/ultimate/V1 - 3Wheeler/Fertigung/Blech-Abdeckung - standard.DXF

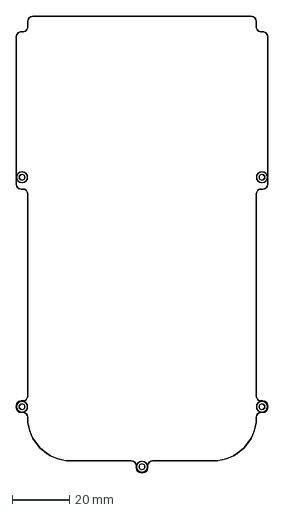
[picture p136: CAD file, 2019-10-27]
Teilnehmer/ultimate/V1 - 3Wheeler/Fertigung/Blech-Abdeckung - standard.DXF
87.8 x 159.5 mm
