ultimate/F-OR1/Teilnehmer/ultimate/V3 - 4Wheeler/Antrieb-Rahmen.SLDPRT

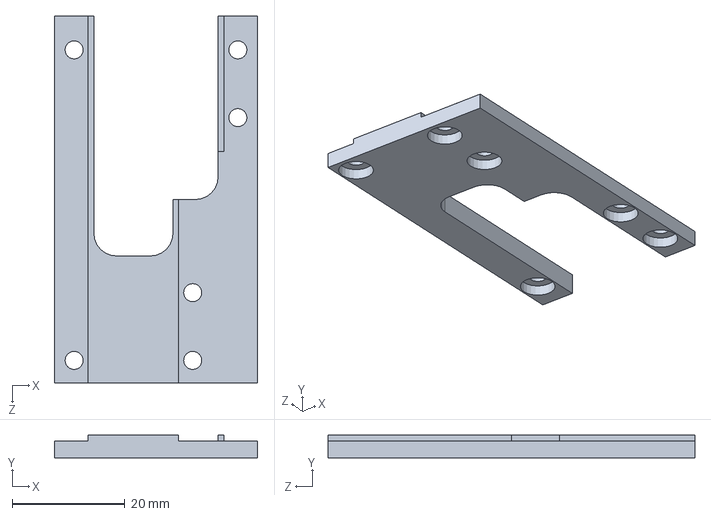
[picture p137: CAD file, 2019-10-27]
Teilnehmer/ultimate/V3 - 4Wheeler/Antrieb-Rahmen.SLDPRT
36.0 x 4.00 x 65.0 mm
