ultimate/F-OR1/Teilnehmer/ultimate/V3 - 4Wheeler/Fertigung/Rad-Nabe-Lenkbar.DXF

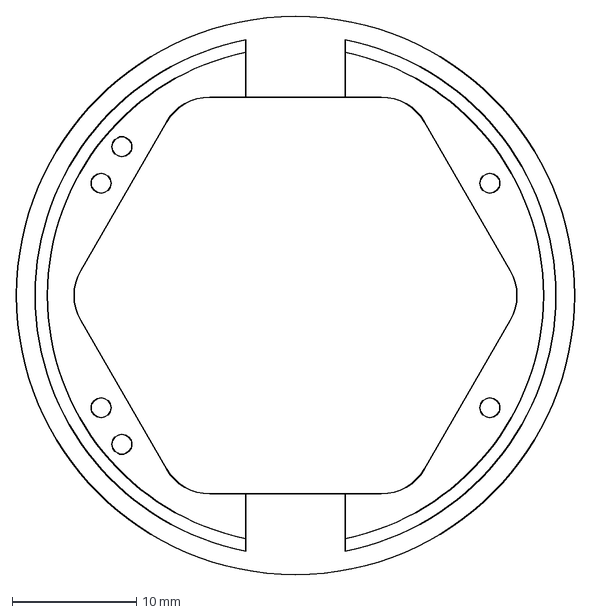
[picture p138: CAD file, 2019-10-27]
Teilnehmer/ultimate/V3 - 4Wheeler/Fertigung/Rad-Nabe-Lenkbar.DXF
45.0 x 45.0 mm
