ultimate/F-OR1/Komponenten/Hobby King X-Car 60A Brushless Car ESC - Lüfter.SLDPRT

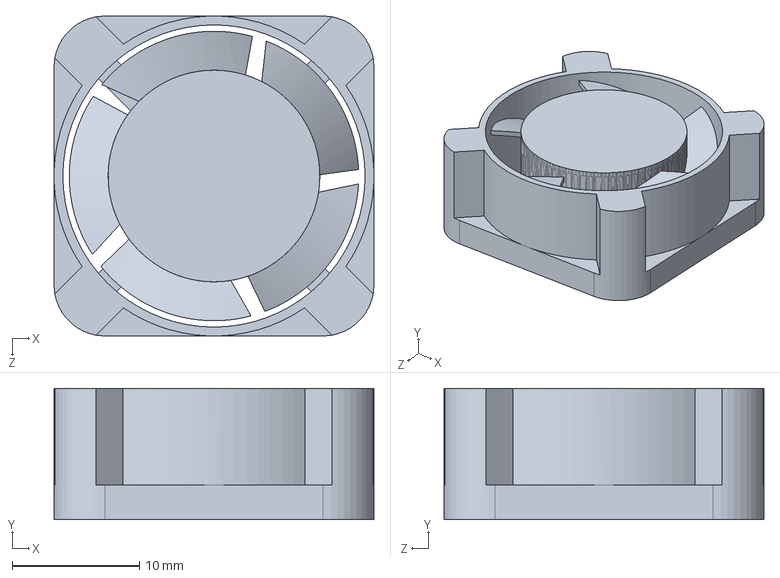
[picture p139: CAD file, 2019-10-27]
Komponenten/Hobby King X-Car 60A Brushless Car ESC - Lüfter.SLDPRT
25.1 x 10.3 x 25.1 mm
