ultimate/F-OR1/Normteile/Kugellager - 61801 6801.SLDPRT

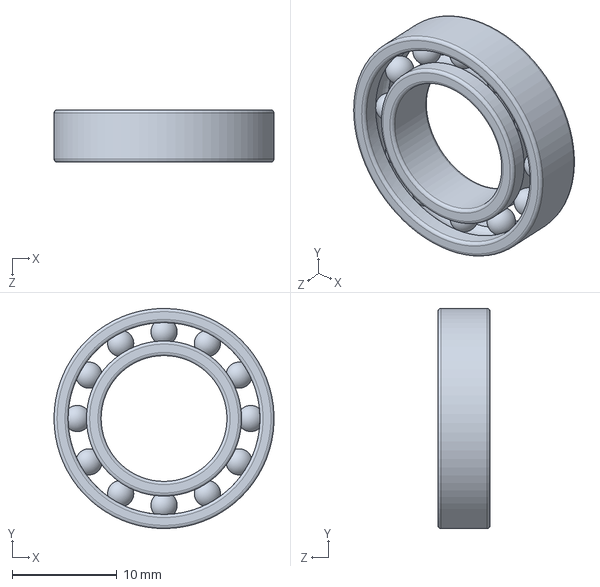
[picture p140: CAD file, 2019-10-27]
Normteile/Kugellager - 61801 6801.SLDPRT
21.0 x 21.0 x 5.00 mm
