ultimate/F-OR1/Teilnehmer/ultimate/Test/Rad.SLDPRT

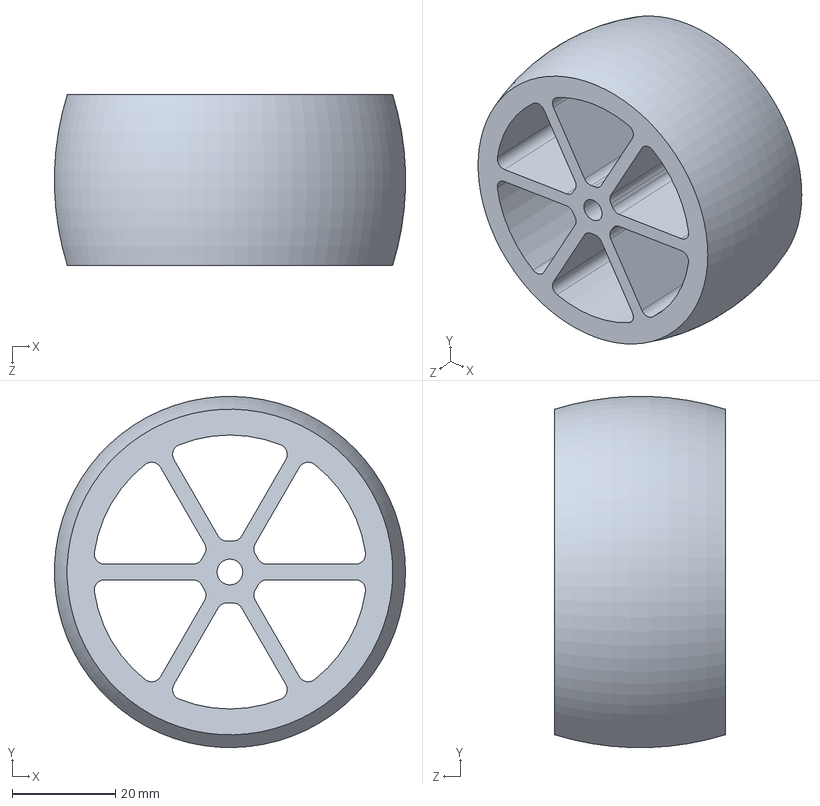
[picture p141: CAD file, 2019-10-27]
Teilnehmer/ultimate/Test/Rad.SLDPRT
67.9 x 67.9 x 33.0 mm
