ultimate/F-OR1/Teilnehmer/ultimate/V1 - 3Wheeler/Antrieb-Halterung.SLDPRT

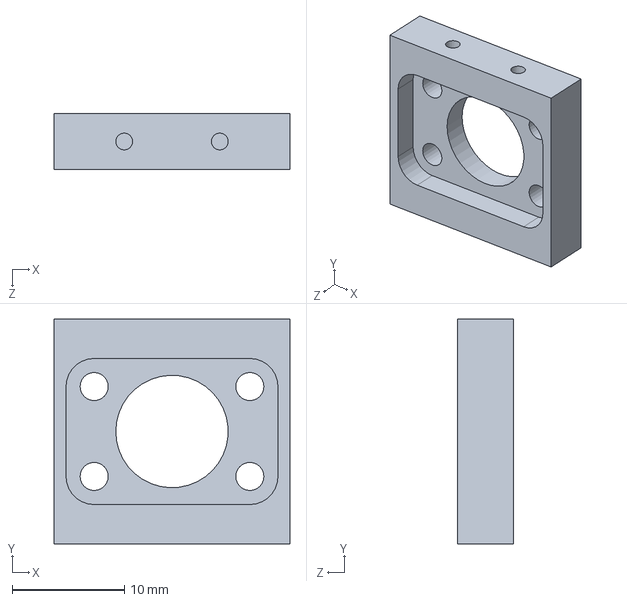
[picture p142: CAD file, 2019-10-27]
Teilnehmer/ultimate/V1 - 3Wheeler/Antrieb-Halterung.SLDPRT
21.0 x 20.0 x 5.00 mm
