ultimate/F-OR1/Teilnehmer/ultimate/V1 - 3Wheeler/Druck/Zahnriemenrad T2.5 B6 Z12 Di4.STL

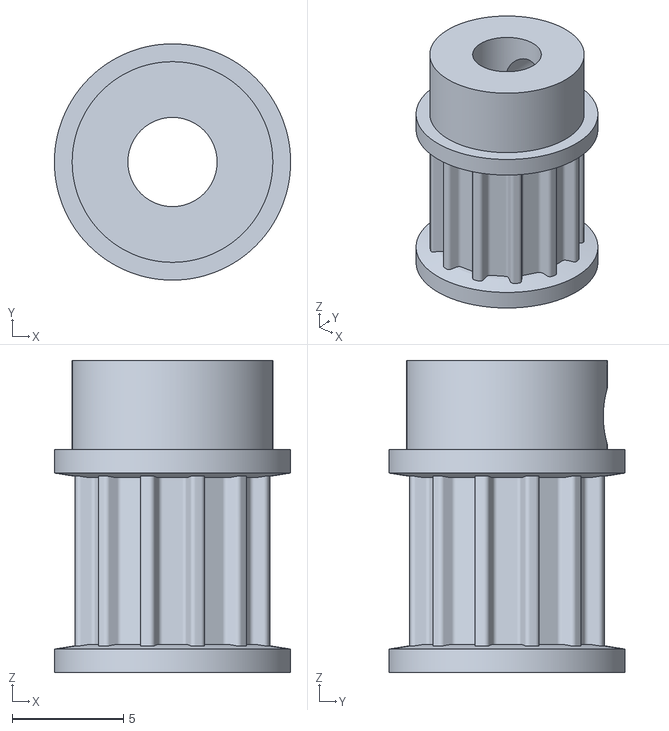
[picture p143: CAD file, 2019-10-27]
Teilnehmer/ultimate/V1 - 3Wheeler/Druck/Zahnriemenrad T2.5 B6 Z12 Di4.STL
10.6 x 10.6 x 14.0
