ultimate/F-OR1/Teilnehmer/ultimate/V2 - Lego/Lego Zahnrad 16Z.SLDPRT

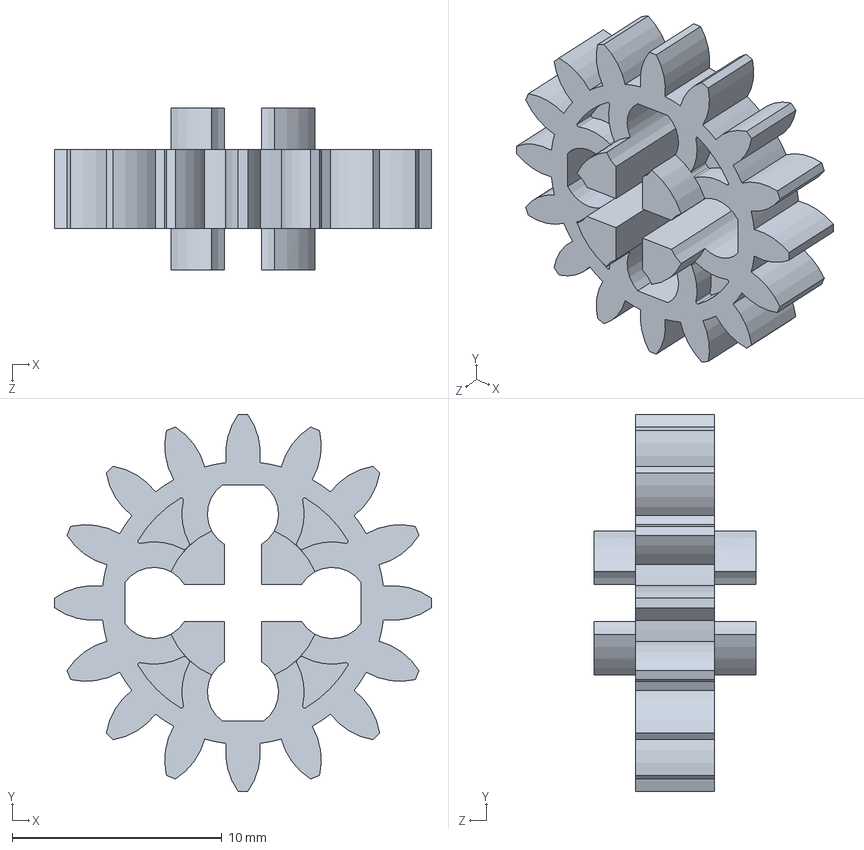
[picture p144: CAD file, 2019-10-27]
Teilnehmer/ultimate/V2 - Lego/Lego Zahnrad 16Z.SLDPRT
18.0 x 18.0 x 7.75 mm
