ultimate/F-OR1/Teilnehmer/ultimate/V3 - 4Wheeler/Export/4-Wheeler - Antrieb-1 Motor_B20-30-24S-FIN-1 Motor_B20-30-24S-FIN-Rotorwelle-1.STL

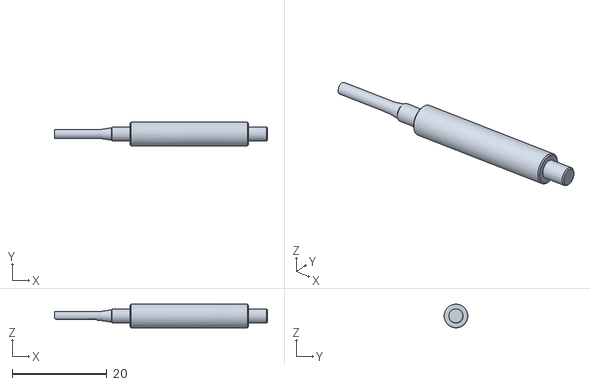
[picture p145: CAD file, 2020-09-06]
Teilnehmer/ultimate/V3 - 4Wheeler/Export/4-Wheeler - Antrieb-1 Motor_B20-30-24S-FIN-1 Motor_B20-30-24S-FIN-Rotorwelle-1.STL
45.0 x 5.00 x 5.00
