ultimate/F-OR1/Teilnehmer/ultimate/V3 - 4Wheeler/Fertigung/Rad-Nabe-Angetrieben.DXF

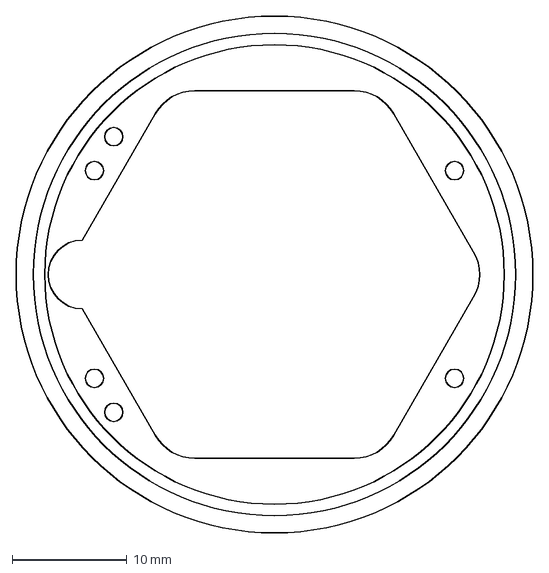
[picture p146: CAD file, 2019-10-27]
Teilnehmer/ultimate/V3 - 4Wheeler/Fertigung/Rad-Nabe-Angetrieben.DXF
45.0 x 45.0 mm
