ultimate/F-OR1/Teilnehmer/ultimate/V3 - 4Wheeler/Rad-Abstandshalter.SLDPRT

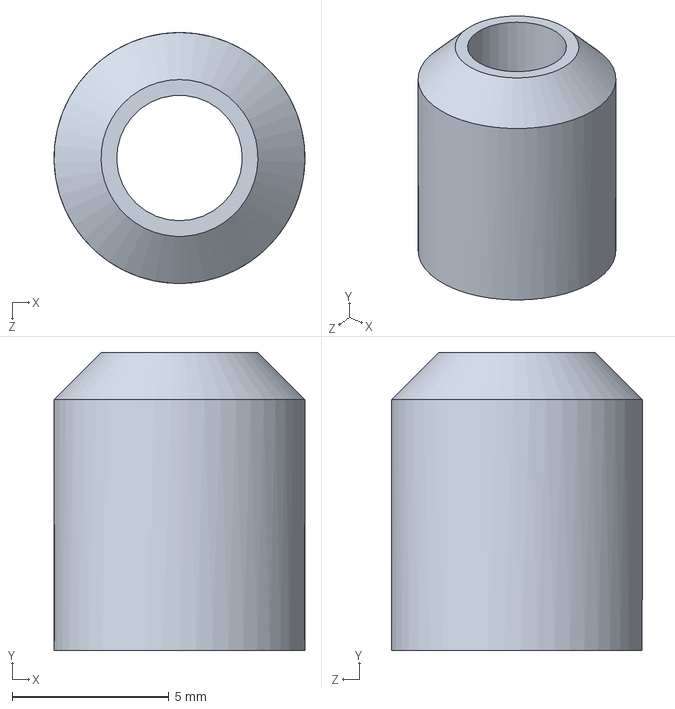
[picture p147: CAD file, 2019-10-27]
Teilnehmer/ultimate/V3 - 4Wheeler/Rad-Abstandshalter.SLDPRT
8.00 x 9.50 x 8.00 mm
