ultimate/F-OR1/Komponenten/Servo-Horn.SLDPRT

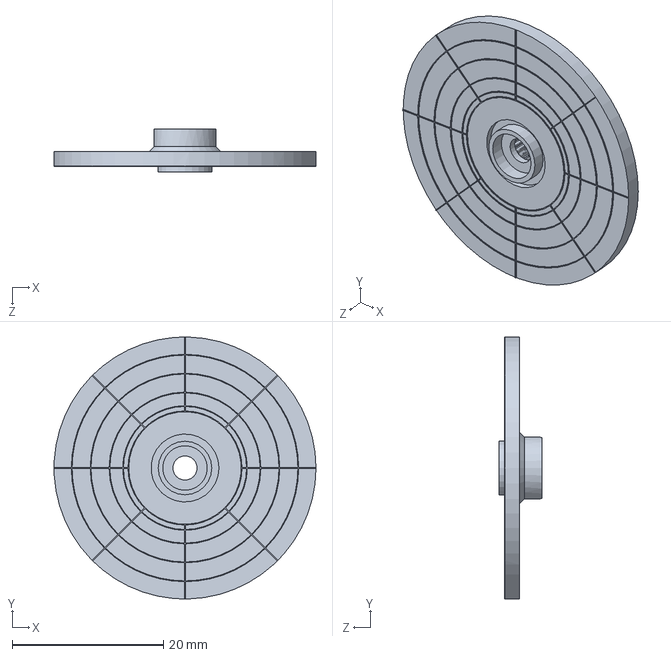
[picture p148: CAD file, 2015-01-06]
Komponenten/Servo-Horn.SLDPRT
34.7 x 34.7 x 5.70 mm
