ultimate/F-OR1/Teilnehmer/ultimate/V1 - 3Wheeler/Rahmen-Antrieb-B.SLDASM

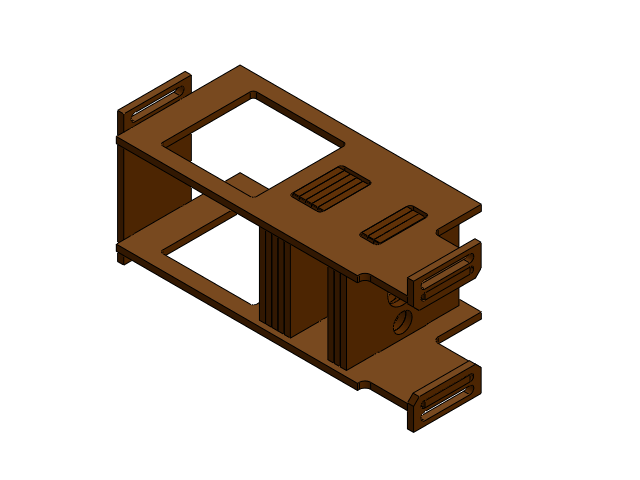
[picture p149: CAD file, 2019-10-27]
Teilnehmer/ultimate/V1 - 3Wheeler/Rahmen-Antrieb-B.SLDASM
Rahmen-Antrieb-B-Platine-Oben x 2
Rahmen-Antrieb-B-Platine-Seite x 8
Rahmen-Antrieb-B-Platine-Anschluss2 x 2
Rahmen-Antrieb-B-Platine-Anschluss1
